AILab-UniversityofTsukuba/Tsukuba-Open-Source-Hand-Prosthesis/Mechanical design/Wrist rotation mechanism/STL/Socket Connector - D_30.STL

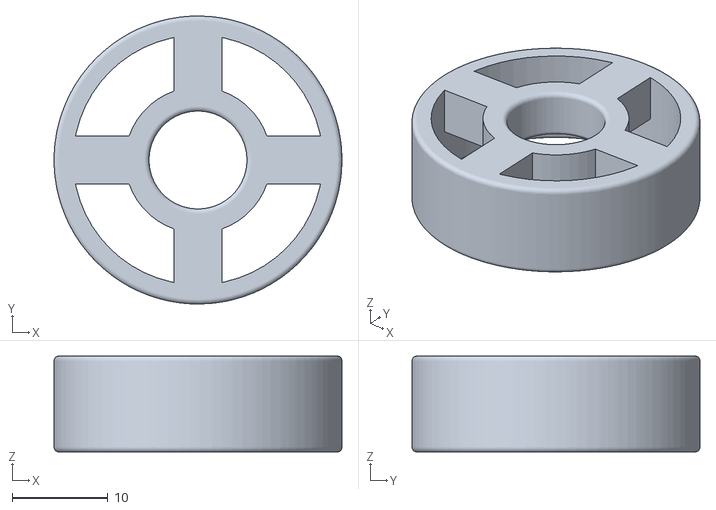
[picture p19: CAD file, 2024-01-24]
Mechanical design/Wrist rotation mechanism/STL/Socket Connector - D_30.STL
30.0 x 30.0 x 10.0
