AILab-UniversityofTsukuba/Tsukuba-Open-Source-Hand-Prosthesis/Mechanical design/Hand /STL/100_R/Thenar eminence - 100_R.STL

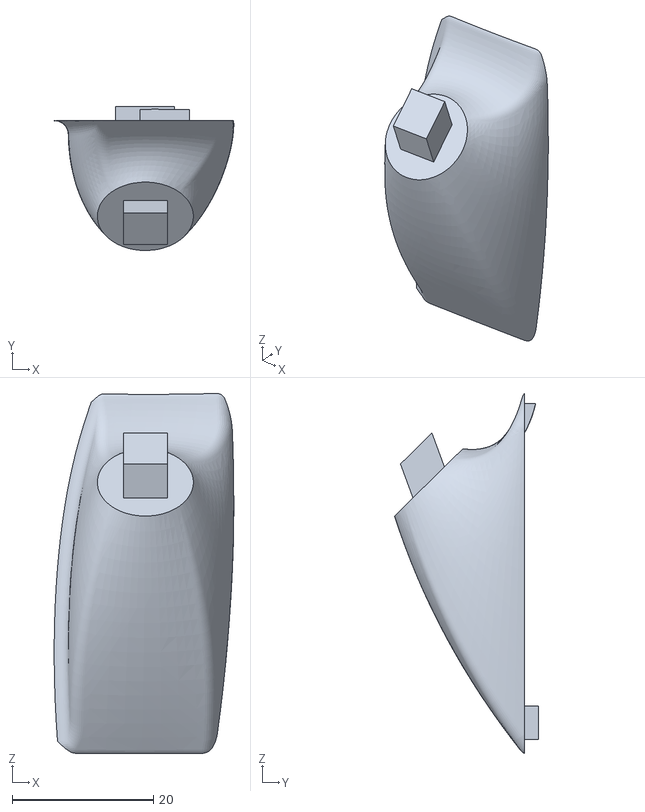
[picture p20: CAD file, 2024-01-24]
Mechanical design/Hand /STL/100_R/Thenar eminence - 100_R.STL
25.4 x 20.4 x 51.0
