AILab-UniversityofTsukuba/Tsukuba-Open-Source-Hand-Prosthesis/Mechanical design/Hand /STL/105_R/Rotation axis - 105_R.STL

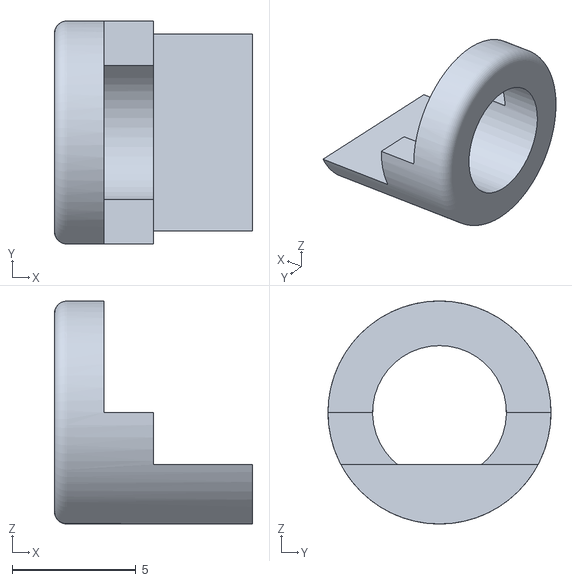
[picture p21: CAD file, 2024-01-24]
Mechanical design/Hand /STL/105_R/Rotation axis - 105_R.STL
8.00 x 9.00 x 9.00
