AILab-UniversityofTsukuba/Tsukuba-Open-Source-Hand-Prosthesis/Mechanical design/Hand /STL/110_R/Ring finger - 110_R.STL

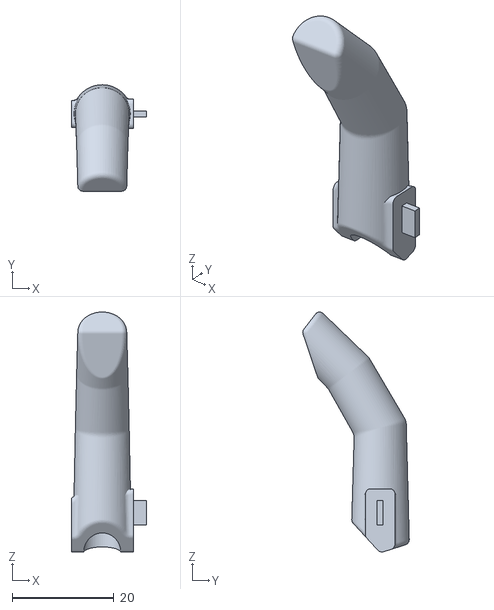
[picture p22: CAD file, 2024-01-24]
Mechanical design/Hand /STL/110_R/Ring finger - 110_R.STL
14.8 x 21.0 x 47.3
