AILab-UniversityofTsukuba/Tsukuba-Open-Source-Hand-Prosthesis/Mechanical design/Hand /STL/115_R/Rotation axis - 115_R.STL

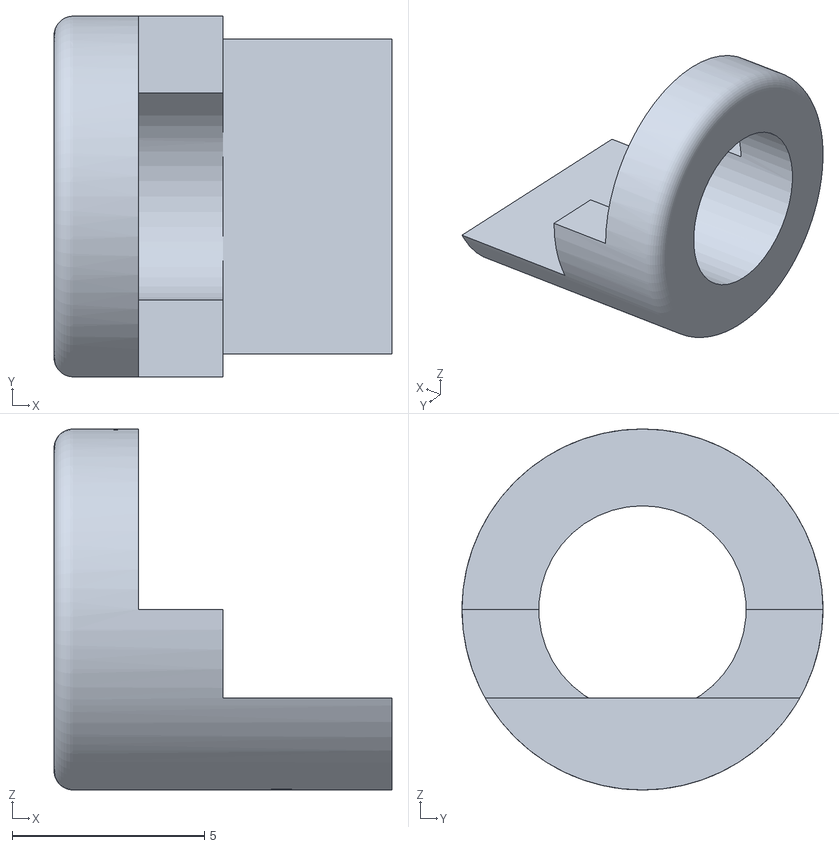
[picture p23: CAD file, 2024-01-24]
Mechanical design/Hand /STL/115_R/Rotation axis - 115_R.STL
8.80 x 9.40 x 9.40
