AILab-UniversityofTsukuba/Tsukuba-Open-Source-Hand-Prosthesis/Mechanical design/Hand /STL/120_R/Index finger - 120_R.STL

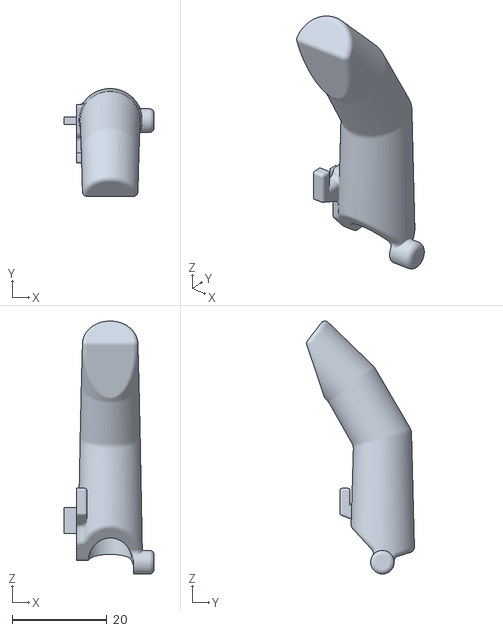
[picture p24: CAD file, 2024-01-24]
Mechanical design/Hand /STL/120_R/Index finger - 120_R.STL
19.1 x 22.8 x 53.4
