AILab-UniversityofTsukuba/Tsukuba-Open-Source-Hand-Prosthesis/Mechanical design/Hand /STL/125_R/Thenar eminence - 125_R.STL

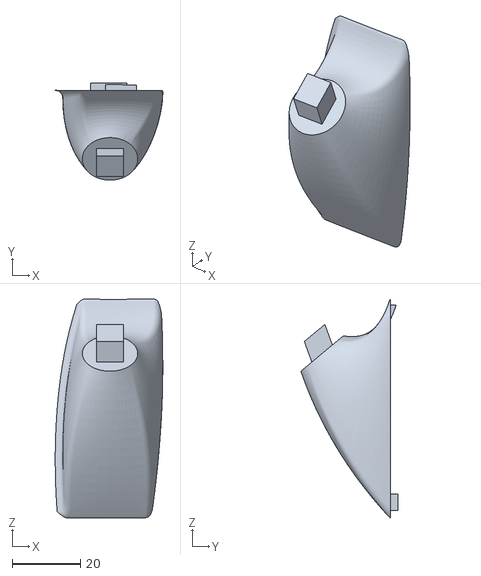
[picture p25: CAD file, 2024-01-24]
Mechanical design/Hand /STL/125_R/Thenar eminence - 125_R.STL
31.5 x 28.5 x 64.1
