AILab-UniversityofTsukuba/Tsukuba-Open-Source-Hand-Prosthesis/Mechanical design/Hand /STL/130_R/Ring finger - 130_R.STL

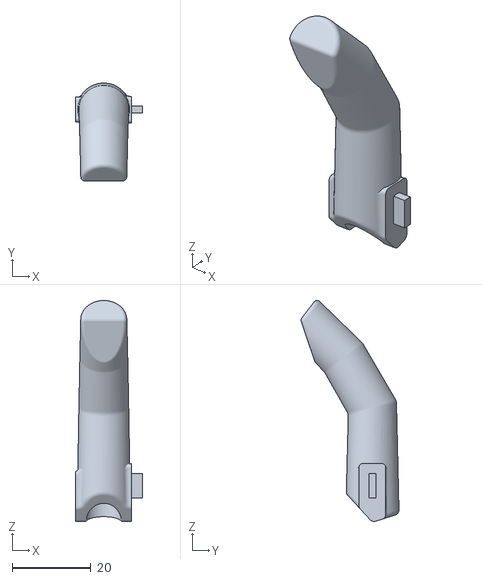
[picture p26: CAD file, 2024-01-24]
Mechanical design/Hand /STL/130_R/Ring finger - 130_R.STL
17.1 x 24.9 x 56.3
