AILab-UniversityofTsukuba/Tsukuba-Open-Source-Hand-Prosthesis/Mechanical design/Hand /STL/135_R/Little finger - 135_R.STL

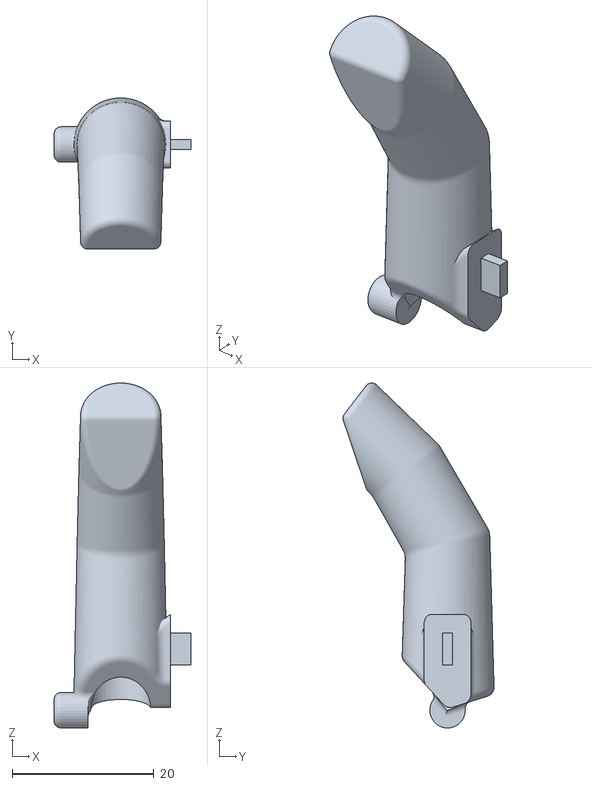
[picture p27: CAD file, 2024-01-24]
Mechanical design/Hand /STL/135_R/Little finger - 135_R.STL
19.3 x 21.3 x 48.6
