AILab-UniversityofTsukuba/Tsukuba-Open-Source-Hand-Prosthesis/Mechanical design/Hand /STL/140_R/Thenar eminence - 140_R.STL

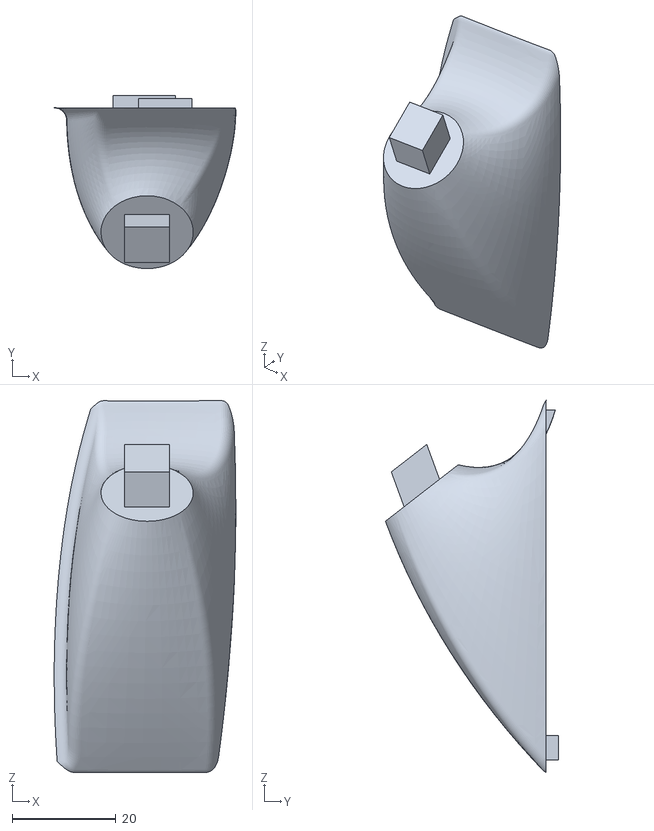
[picture p28: CAD file, 2024-01-24]
Mechanical design/Hand /STL/140_R/Thenar eminence - 140_R.STL
35.1 x 33.4 x 71.8
