AILab-UniversityofTsukuba/Tsukuba-Open-Source-Hand-Prosthesis/Mechanical design/Hand /STL/145_R/Ring finger - 145_R.STL

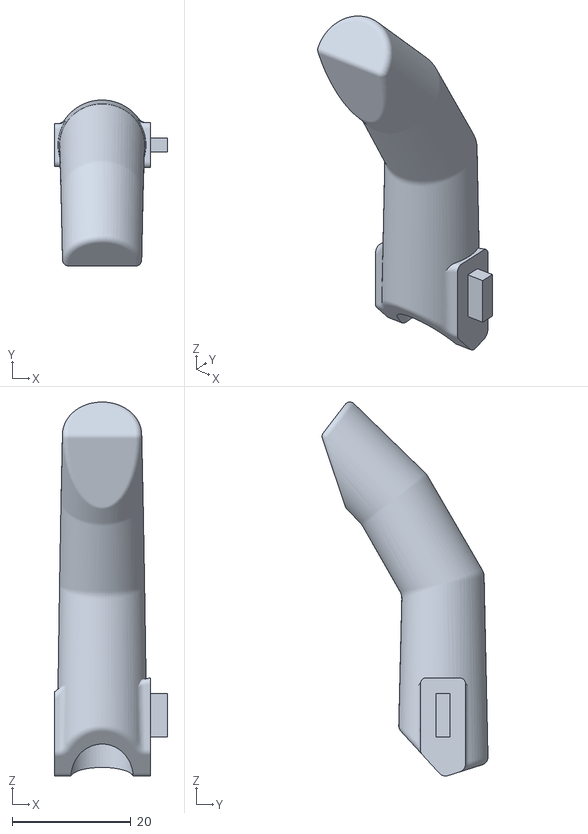
[picture p29: CAD file, 2024-01-24]
Mechanical design/Hand /STL/145_R/Ring finger - 145_R.STL
19.0 x 27.9 x 62.9
