AILab-UniversityofTsukuba/Tsukuba-Open-Source-Hand-Prosthesis/Mechanical design/Hand /STL/150_R/Lid - 150_R.STL

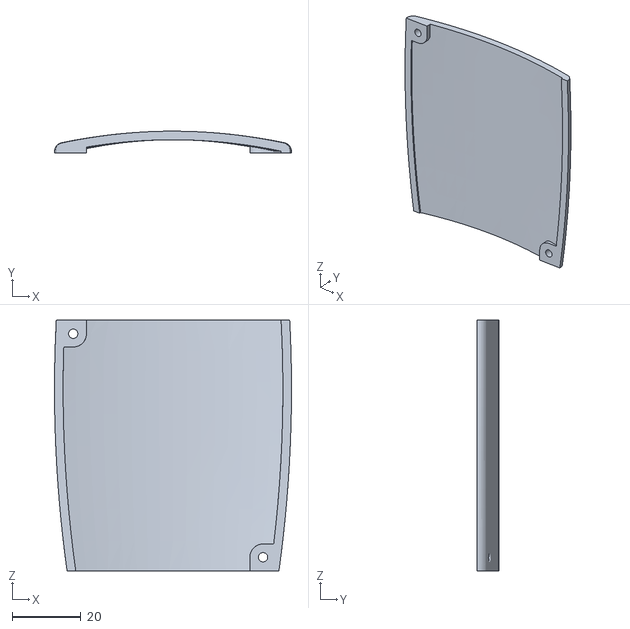
[picture p30: CAD file, 2024-01-24]
Mechanical design/Hand /STL/150_R/Lid - 150_R.STL
68.8 x 6.30 x 72.8
