AILab-UniversityofTsukuba/Tsukuba-Open-Source-Hand-Prosthesis/Mechanical design/Wrist rotation mechanism/STL/Socket Connector - D_35.STL

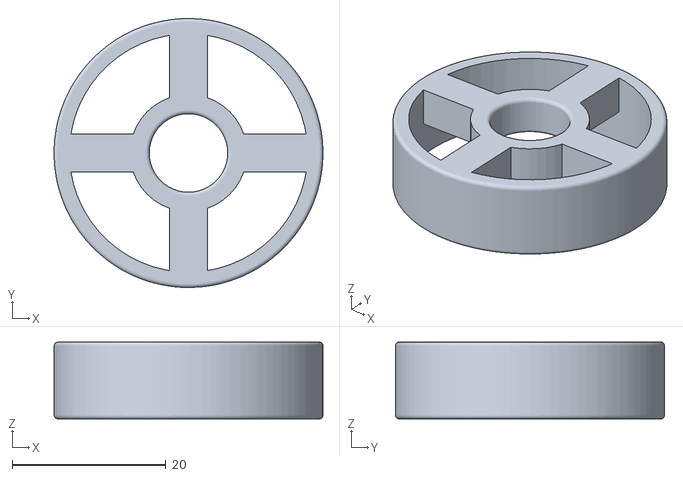
[picture p31: CAD file, 2024-01-24]
Mechanical design/Wrist rotation mechanism/STL/Socket Connector - D_35.STL
35.0 x 35.0 x 10.0
