AILab-UniversityofTsukuba/Tsukuba-Open-Source-Hand-Prosthesis/Mechanical design/Hand /CAD/Palm_structure_5.SLDPRT

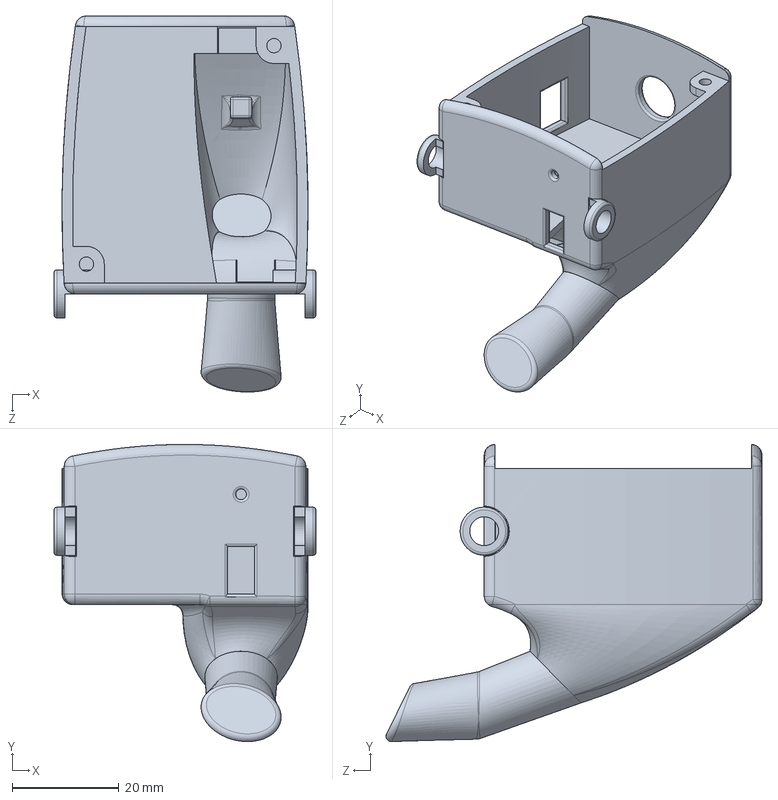
[picture p32: CAD file, 2024-01-24]
Mechanical design/Hand /CAD/Palm_structure_5.SLDPRT
49.0 x 55.6 x 70.4 mm
