AILab-UniversityofTsukuba/Tsukuba-Open-Source-Hand-Prosthesis/Mechanical design/Hand /STL/100_R/Middle finger - 100_R.STL

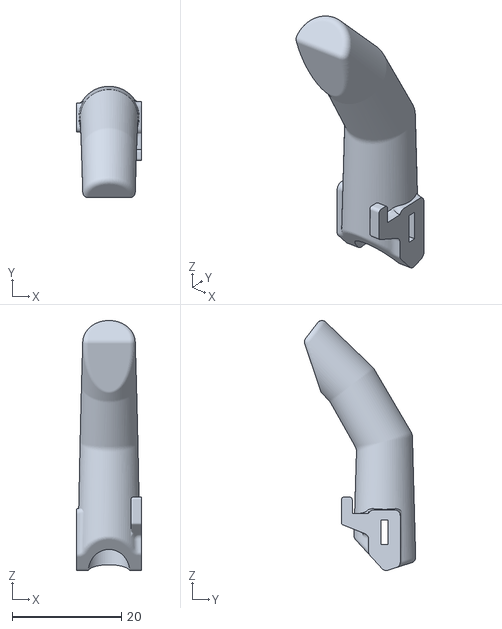
[picture p33: CAD file, 2024-01-24]
Mechanical design/Hand /STL/100_R/Middle finger - 100_R.STL
12.0 x 20.4 x 45.8
