AILab-UniversityofTsukuba/Tsukuba-Open-Source-Hand-Prosthesis/Mechanical design/Hand /STL/105_R/Middle finger - 105_R.STL

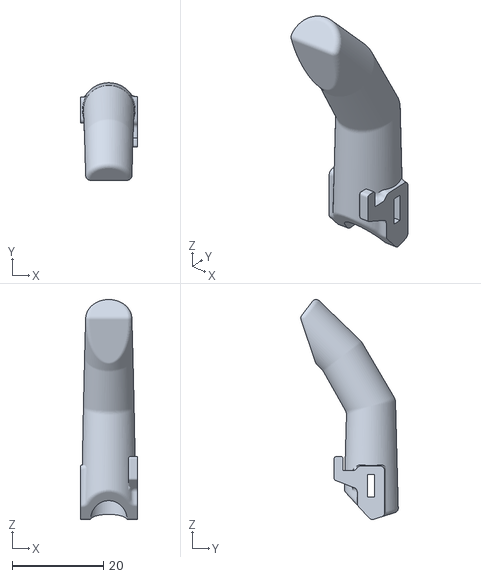
[picture p34: CAD file, 2024-01-24]
Mechanical design/Hand /STL/105_R/Middle finger - 105_R.STL
12.5 x 21.4 x 48.2
