AILab-UniversityofTsukuba/Tsukuba-Open-Source-Hand-Prosthesis/Mechanical design/Hand /STL/110_R/Palm - 110_R.STL

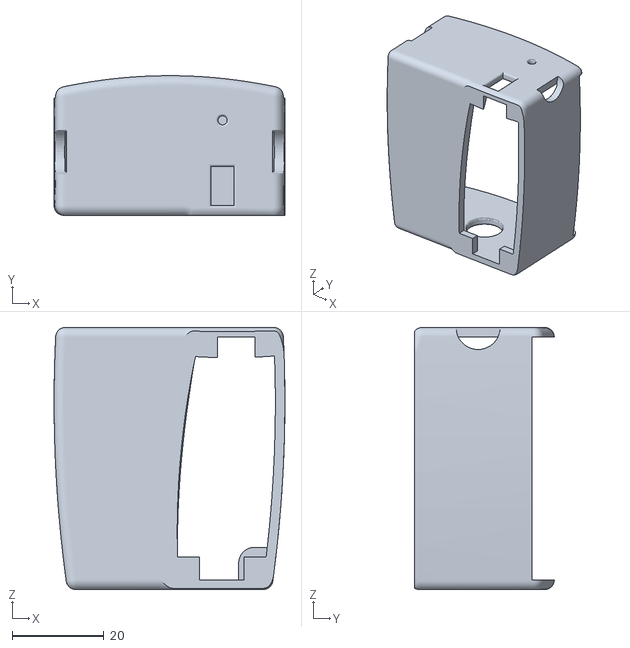
[picture p35: CAD file, 2024-01-24]
Mechanical design/Hand /STL/110_R/Palm - 110_R.STL
50.4 x 30.5 x 57.2
