AILab-UniversityofTsukuba/Tsukuba-Open-Source-Hand-Prosthesis/Mechanical design/Hand /STL/115_R/Little finger - 115_R.STL

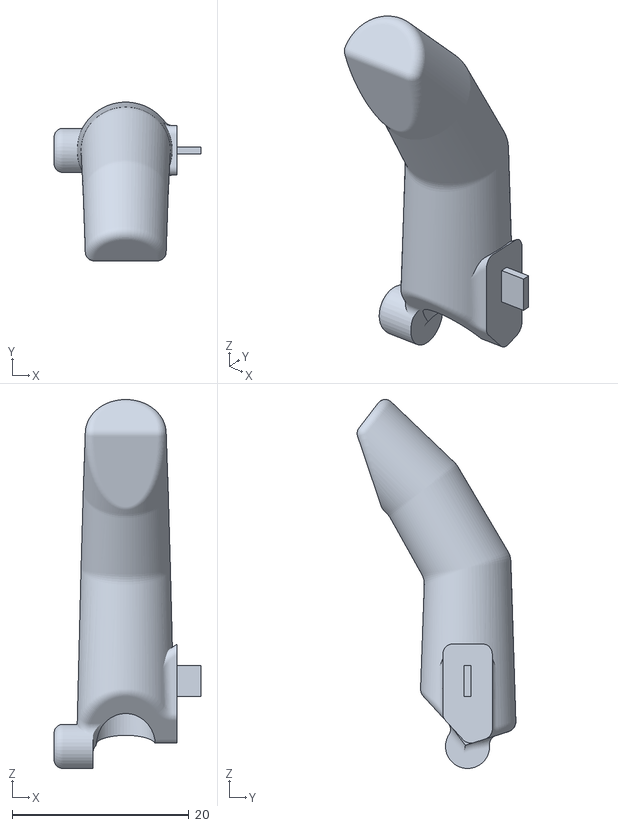
[picture p36: CAD file, 2024-01-24]
Mechanical design/Hand /STL/115_R/Little finger - 115_R.STL
16.6 x 17.9 x 41.7
