AILab-UniversityofTsukuba/Tsukuba-Open-Source-Hand-Prosthesis/Mechanical design/Hand /STL/120_R/Thumb - 120_R.STL

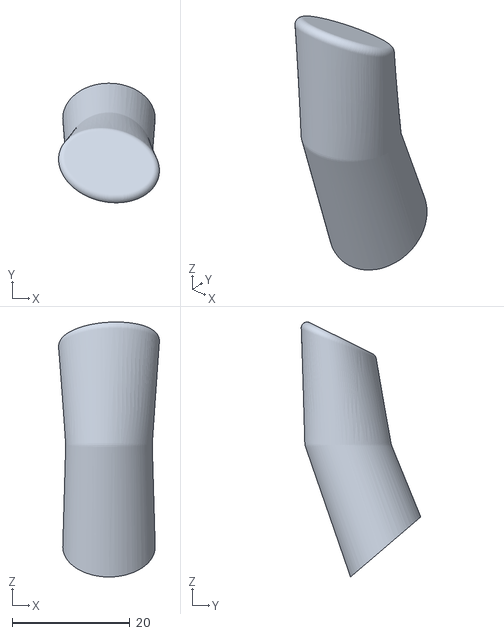
[picture p37: CAD file, 2024-01-24]
Mechanical design/Hand /STL/120_R/Thumb - 120_R.STL
17.1 x 20.3 x 43.3
