AILab-UniversityofTsukuba/Tsukuba-Open-Source-Hand-Prosthesis/Mechanical design/Hand /STL/125_R/Thumb - 125_R.STL

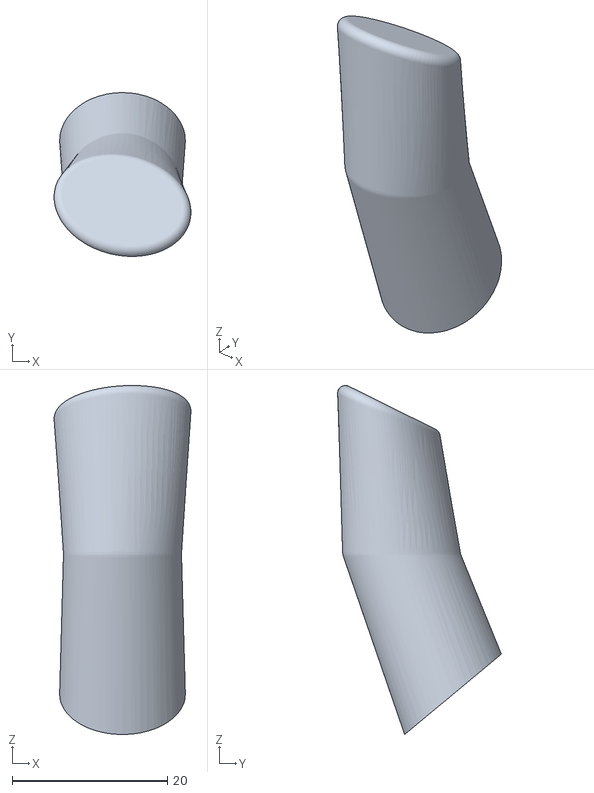
[picture p38: CAD file, 2024-01-24]
Mechanical design/Hand /STL/125_R/Thumb - 125_R.STL
17.6 x 21.1 x 44.9
