AILab-UniversityofTsukuba/Tsukuba-Open-Source-Hand-Prosthesis/Mechanical design/Hand /STL/130_R/Lid - 130_R.STL

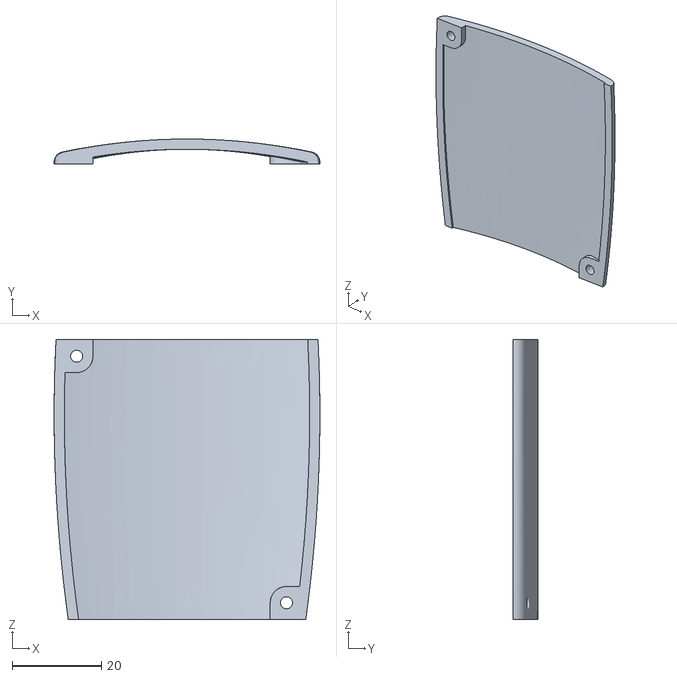
[picture p39: CAD file, 2024-01-24]
Mechanical design/Hand /STL/130_R/Lid - 130_R.STL
59.6 x 5.60 x 62.8
