AILab-UniversityofTsukuba/Tsukuba-Open-Source-Hand-Prosthesis/Mechanical design/Hand /STL/135_R/Thumb - 135_R.STL

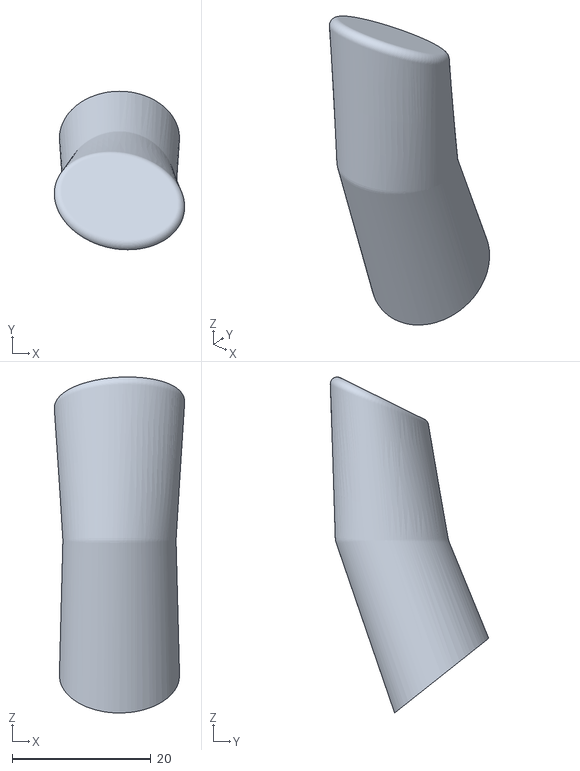
[picture p40: CAD file, 2024-01-24]
Mechanical design/Hand /STL/135_R/Thumb - 135_R.STL
18.8 x 22.8 x 48.4
