AILab-UniversityofTsukuba/Tsukuba-Open-Source-Hand-Prosthesis/Mechanical design/Hand /STL/140_R/Palm - 140_R.STL

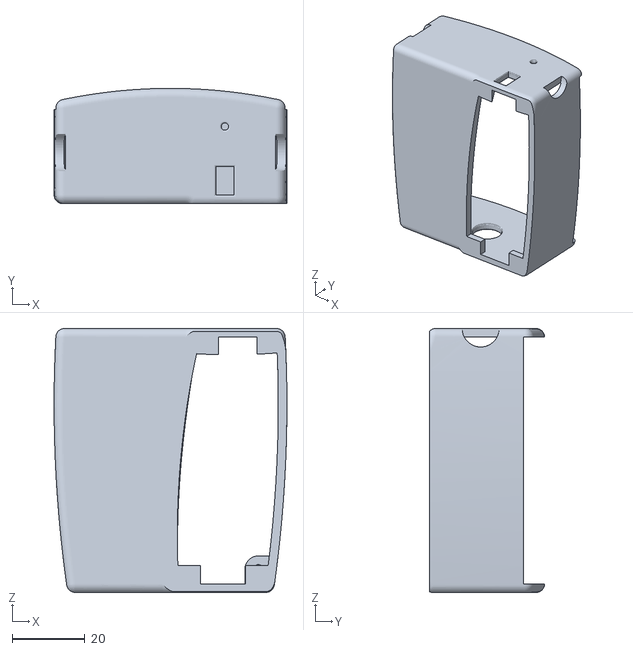
[picture p41: CAD file, 2024-01-24]
Mechanical design/Hand /STL/140_R/Palm - 140_R.STL
64.2 x 31.8 x 72.8
