AILab-UniversityofTsukuba/Tsukuba-Open-Source-Hand-Prosthesis/Mechanical design/Hand /STL/145_R/Rotation axis - 145_R.STL

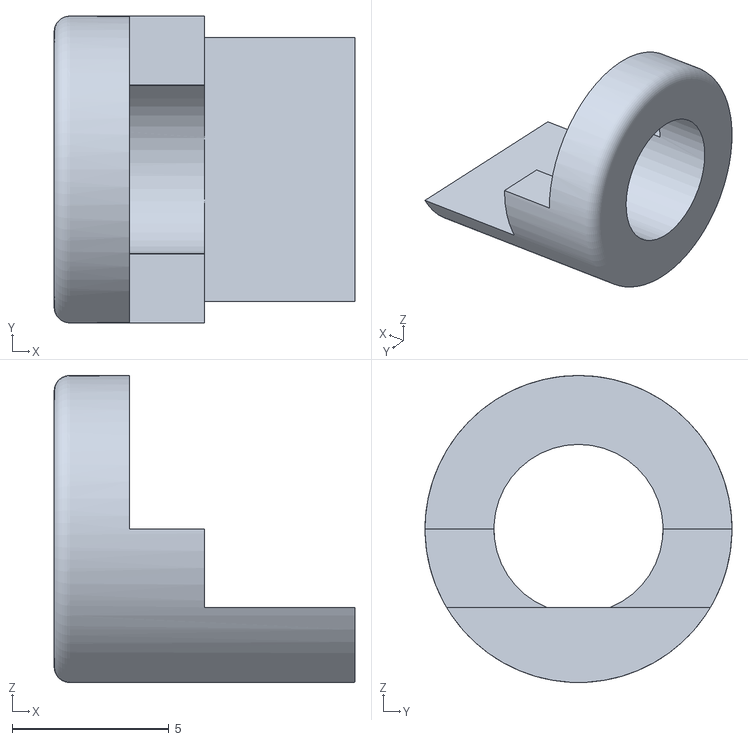
[picture p42: CAD file, 2024-01-24]
Mechanical design/Hand /STL/145_R/Rotation axis - 145_R.STL
9.60 x 9.80 x 9.80
