AILab-UniversityofTsukuba/Tsukuba-Open-Source-Hand-Prosthesis/Mechanical design/Hand /STL/150_R/Index finger - 150_R.STL

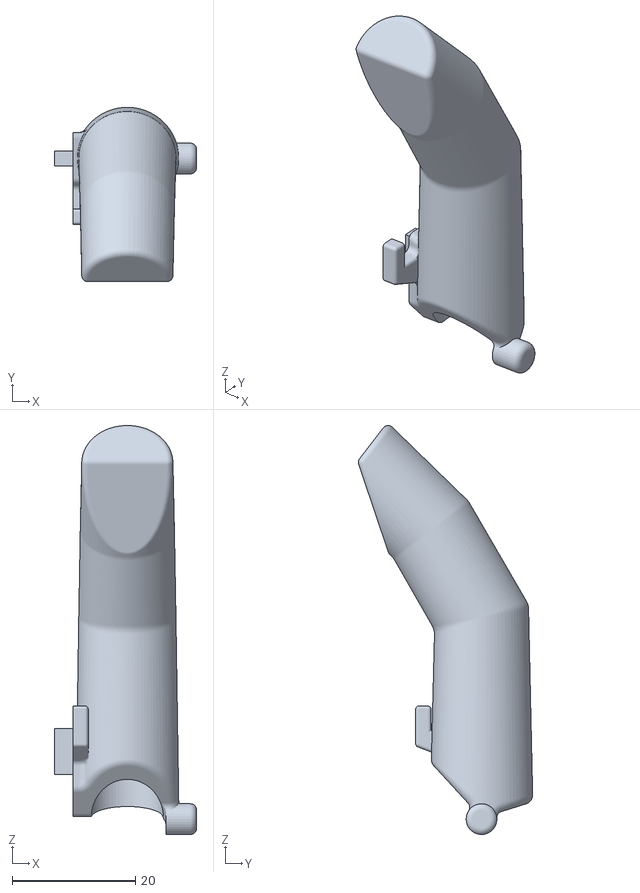
[picture p43: CAD file, 2024-01-24]
Mechanical design/Hand /STL/150_R/Index finger - 150_R.STL
23.1 x 28.3 x 66.5
