AILab-UniversityofTsukuba/Tsukuba-Open-Source-Hand-Prosthesis/Mechanical design/Hand /STL/105_R/Thenar eminence - 105_R.STL

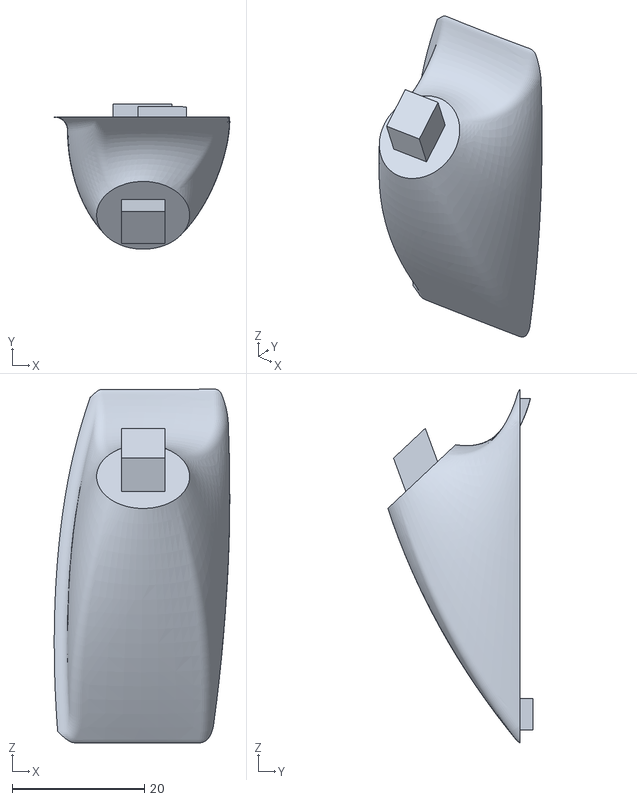
[picture p44: CAD file, 2024-01-24]
Mechanical design/Hand /STL/105_R/Thenar eminence - 105_R.STL
26.6 x 22.0 x 53.6
