AILab-UniversityofTsukuba/Tsukuba-Open-Source-Hand-Prosthesis/Mechanical design/Hand /STL/110_R/Lid - 110_R.STL

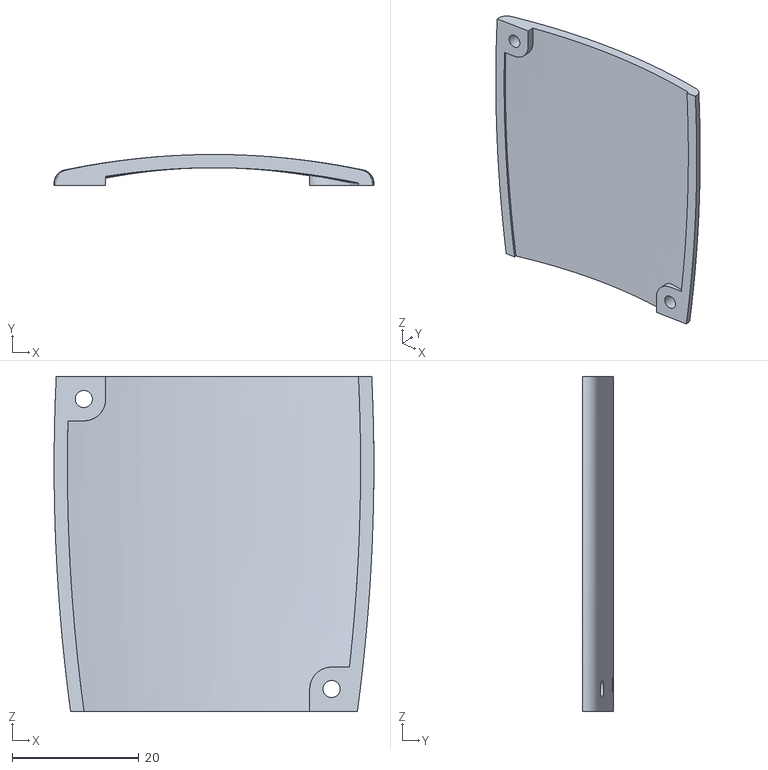
[picture p45: CAD file, 2024-01-24]
Mechanical design/Hand /STL/110_R/Lid - 110_R.STL
50.4 x 4.90 x 52.8
