AILab-UniversityofTsukuba/Tsukuba-Open-Source-Hand-Prosthesis/Mechanical design/Hand /STL/115_R/Thenar eminence - 115_R.STL

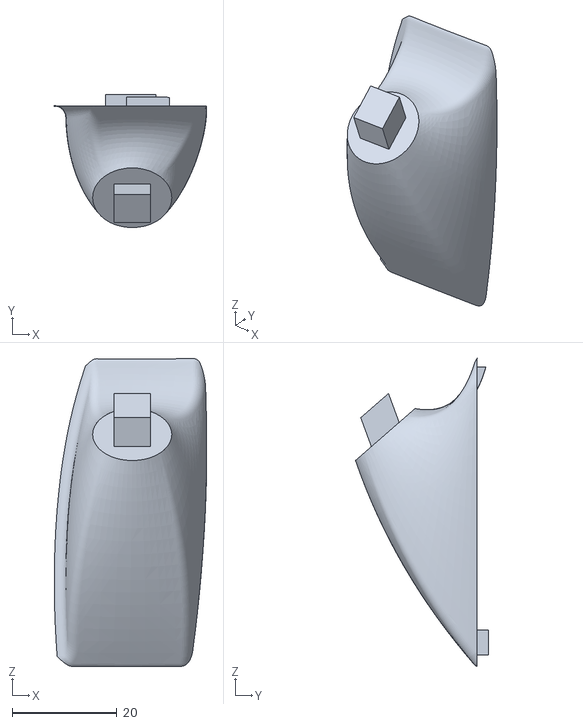
[picture p46: CAD file, 2024-01-24]
Mechanical design/Hand /STL/115_R/Thenar eminence - 115_R.STL
29.1 x 25.4 x 58.8
