AILab-UniversityofTsukuba/Tsukuba-Open-Source-Hand-Prosthesis/Mechanical design/Hand /STL/120_R/Lid - 120_R.STL

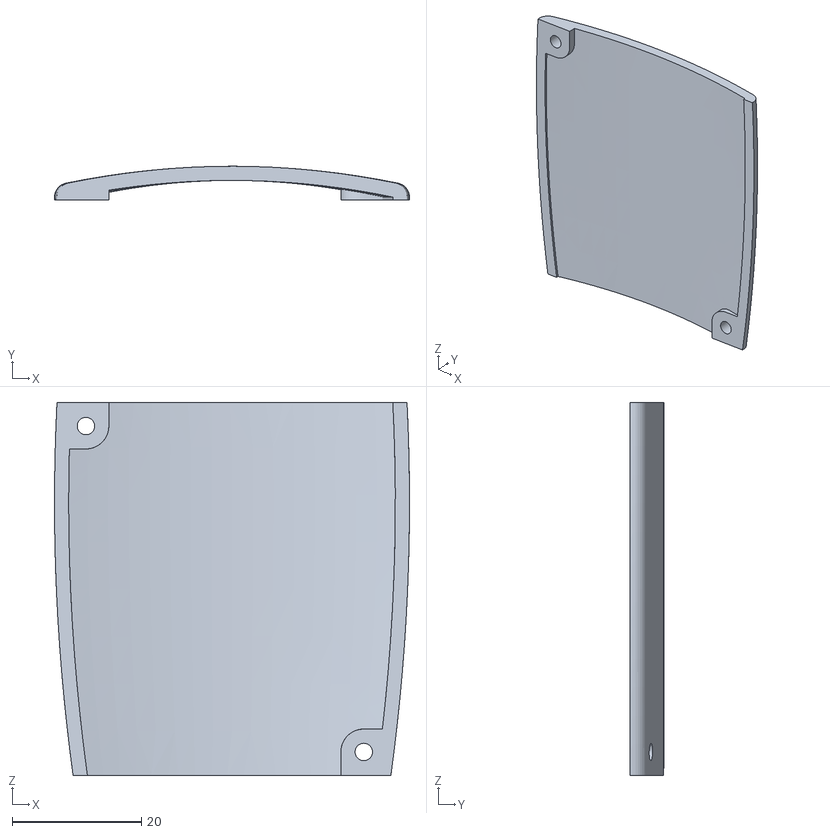
[picture p47: CAD file, 2024-01-24]
Mechanical design/Hand /STL/120_R/Lid - 120_R.STL
55.0 x 5.20 x 57.8
