AILab-UniversityofTsukuba/Tsukuba-Open-Source-Hand-Prosthesis/Mechanical design/Hand /STL/125_R/Middle finger - 125_R.STL

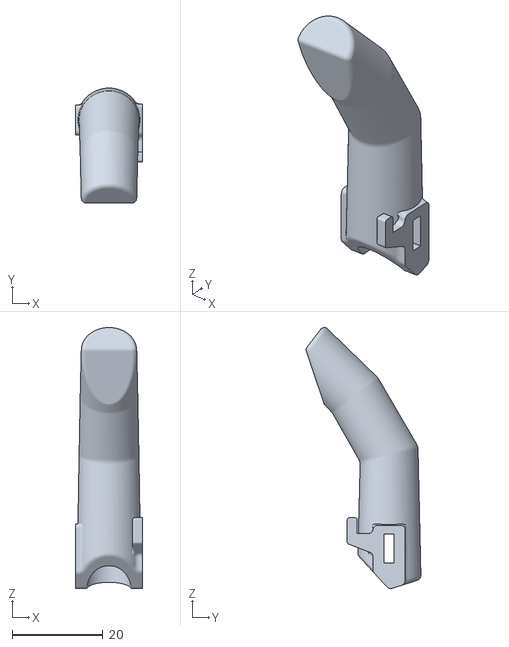
[picture p48: CAD file, 2024-01-24]
Mechanical design/Hand /STL/125_R/Middle finger - 125_R.STL
14.8 x 25.3 x 57.6
