AILab-UniversityofTsukuba/Tsukuba-Open-Source-Hand-Prosthesis/Mechanical design/Hand /STL/130_R/Index finger - 130_R.STL

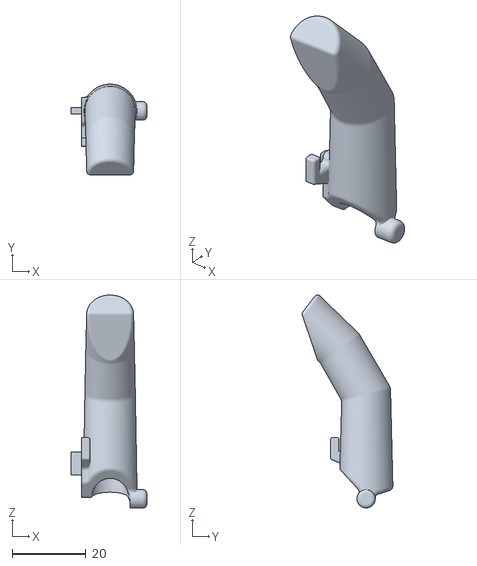
[picture p49: CAD file, 2024-01-24]
Mechanical design/Hand /STL/130_R/Index finger - 130_R.STL
20.5 x 24.6 x 57.8
