AILab-UniversityofTsukuba/Tsukuba-Open-Source-Hand-Prosthesis/Mechanical design/Hand /STL/135_R/Lid - 135_R.STL

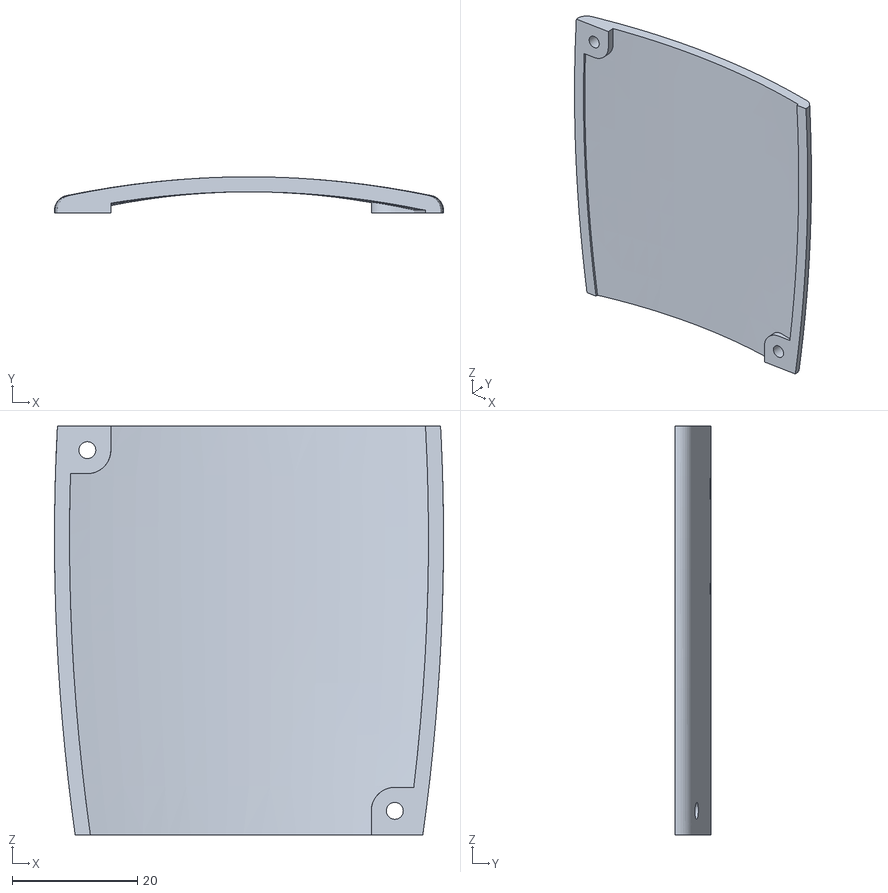
[picture p50: CAD file, 2024-01-24]
Mechanical design/Hand /STL/135_R/Lid - 135_R.STL
62.0 x 5.80 x 65.2
