AILab-UniversityofTsukuba/Tsukuba-Open-Source-Hand-Prosthesis/Mechanical design/Hand /STL/140_R/Ring finger - 140_R.STL

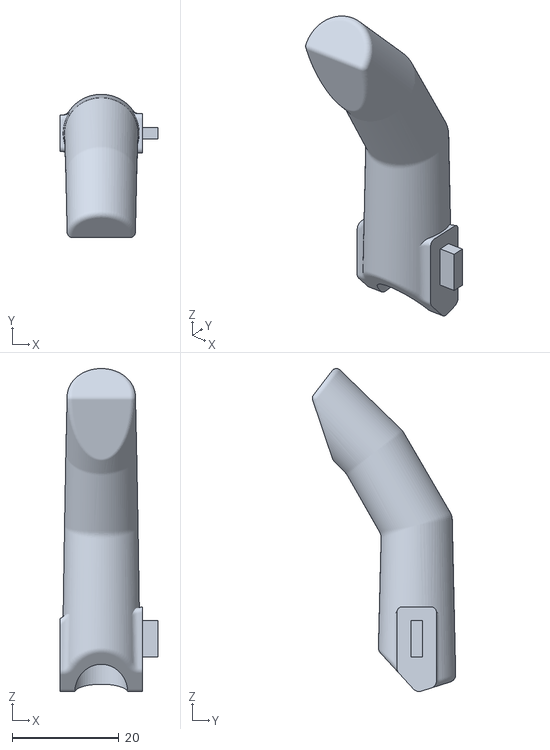
[picture p51: CAD file, 2024-01-24]
Mechanical design/Hand /STL/140_R/Ring finger - 140_R.STL
18.4 x 26.9 x 60.6
