AILab-UniversityofTsukuba/Tsukuba-Open-Source-Hand-Prosthesis/Mechanical design/Hand /STL/145_R/Lid - 145_R.STL

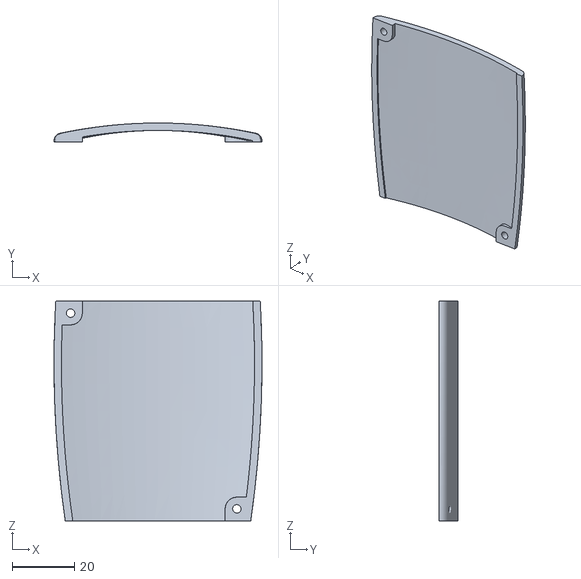
[picture p52: CAD file, 2024-01-24]
Mechanical design/Hand /STL/145_R/Lid - 145_R.STL
66.6 x 6.10 x 70.4
