AILab-UniversityofTsukuba/Tsukuba-Open-Source-Hand-Prosthesis/Mechanical design/Hand /STL/150_R/Little finger - 150_R.STL

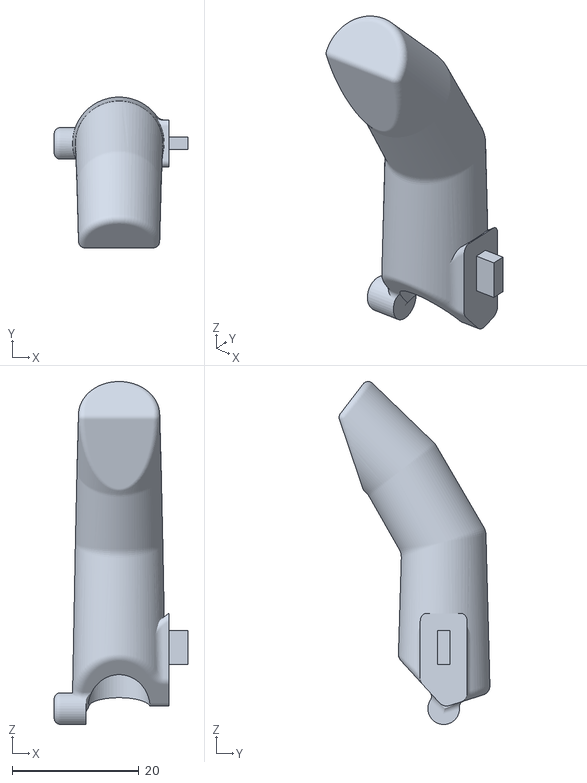
[picture p53: CAD file, 2024-01-24]
Mechanical design/Hand /STL/150_R/Little finger - 150_R.STL
21.1 x 23.8 x 54.1
