AILab-UniversityofTsukuba/Tsukuba-Open-Source-Hand-Prosthesis/Mechanical design/Wrist rotation mechanism/STL/Socket Connector - D_20.STL

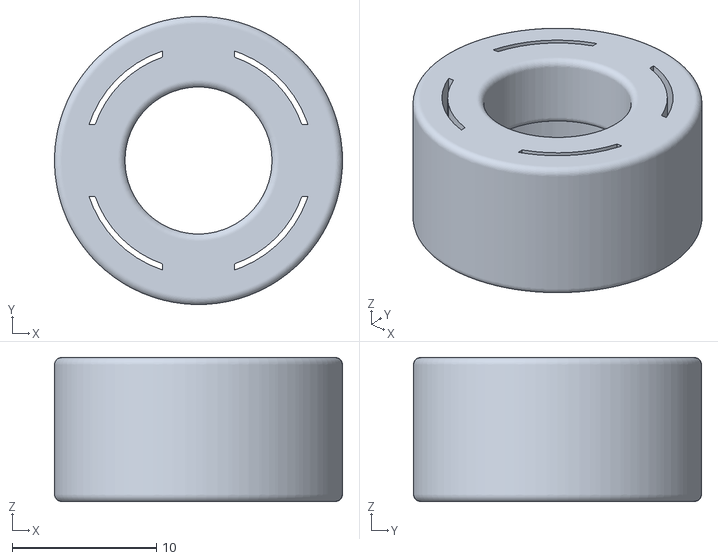
[picture p54: CAD file, 2024-01-24]
Mechanical design/Wrist rotation mechanism/STL/Socket Connector - D_20.STL
20.0 x 20.0 x 10.0
