AILab-UniversityofTsukuba/Tsukuba-Open-Source-Hand-Prosthesis/Mechanical design/Hand /STL/100_R/Lid - 100_R.STL

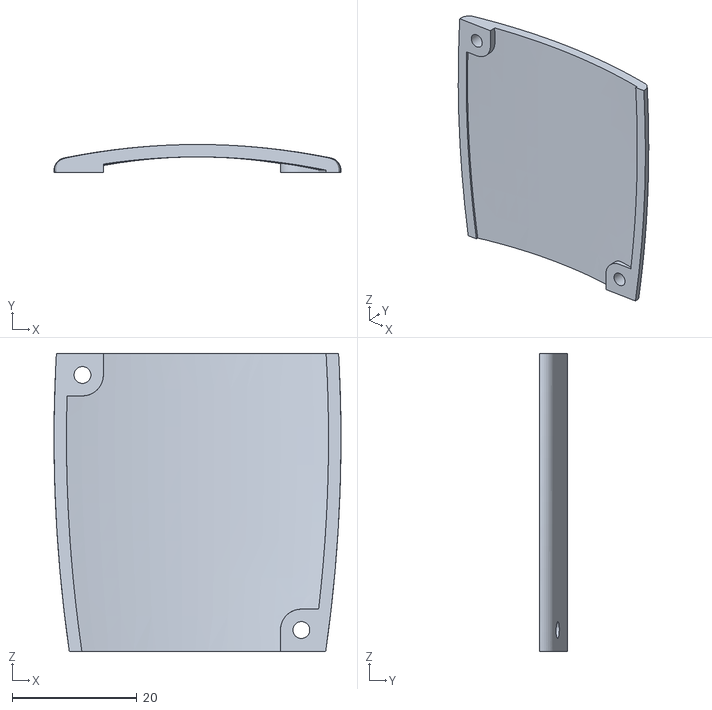
[picture p55: CAD file, 2024-01-24]
Mechanical design/Hand /STL/100_R/Lid - 100_R.STL
46.0 x 4.50 x 47.8
