AILab-UniversityofTsukuba/Tsukuba-Open-Source-Hand-Prosthesis/Mechanical design/Hand /STL/105_R/Ring finger - 105_R.STL

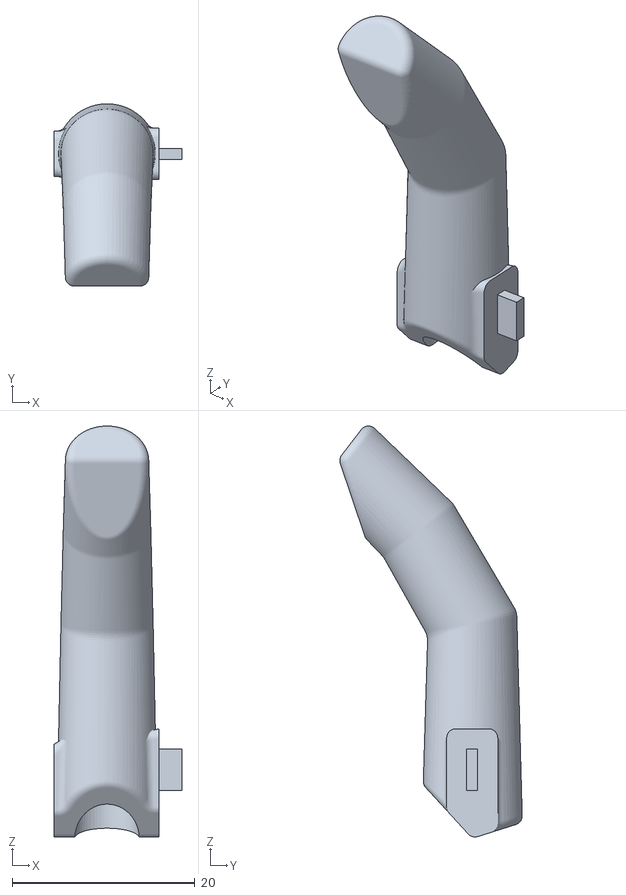
[picture p56: CAD file, 2024-01-24]
Mechanical design/Hand /STL/105_R/Ring finger - 105_R.STL
14.0 x 20.0 x 45.0
