AILab-UniversityofTsukuba/Tsukuba-Open-Source-Hand-Prosthesis/Mechanical design/Hand /STL/110_R/Thenar eminence - 110_R.STL

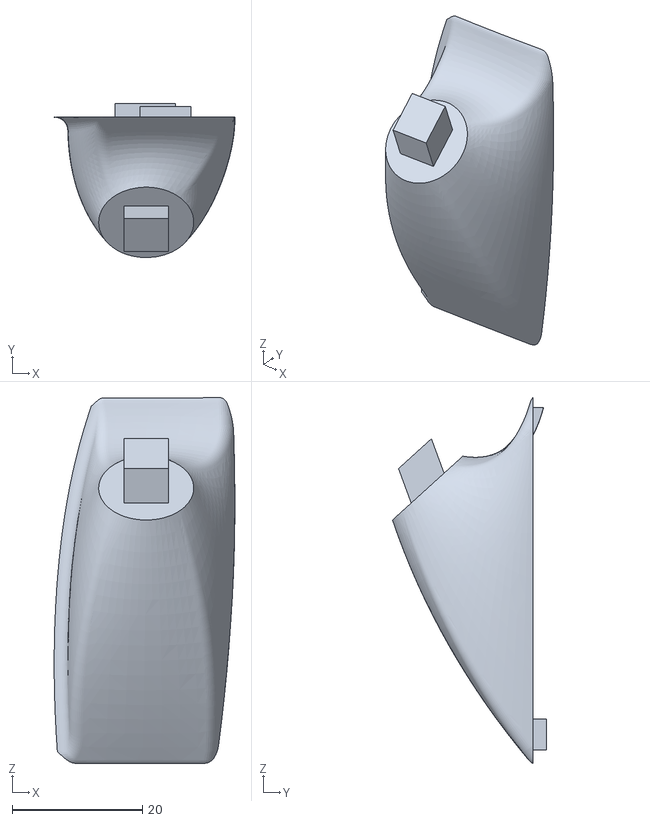
[picture p57: CAD file, 2024-01-24]
Mechanical design/Hand /STL/110_R/Thenar eminence - 110_R.STL
27.8 x 23.7 x 56.2
