AILab-UniversityofTsukuba/Tsukuba-Open-Source-Hand-Prosthesis/Mechanical design/Hand /STL/115_R/Middle finger - 115_R.STL

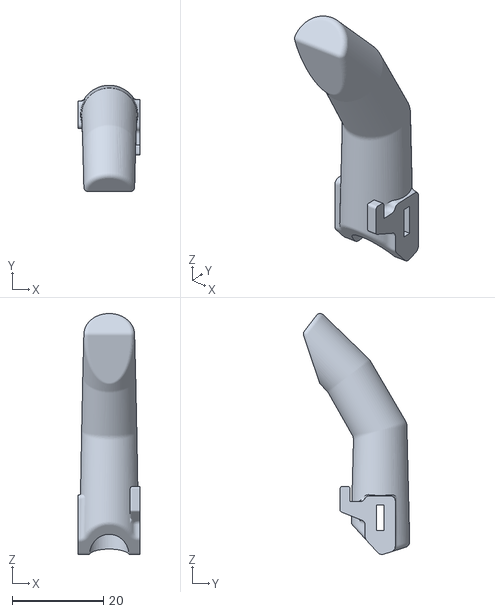
[picture p58: CAD file, 2024-01-24]
Mechanical design/Hand /STL/115_R/Middle finger - 115_R.STL
13.7 x 23.3 x 52.8
