AILab-UniversityofTsukuba/Tsukuba-Open-Source-Hand-Prosthesis/Mechanical design/Hand /STL/125_R/Index finger - 125_R.STL

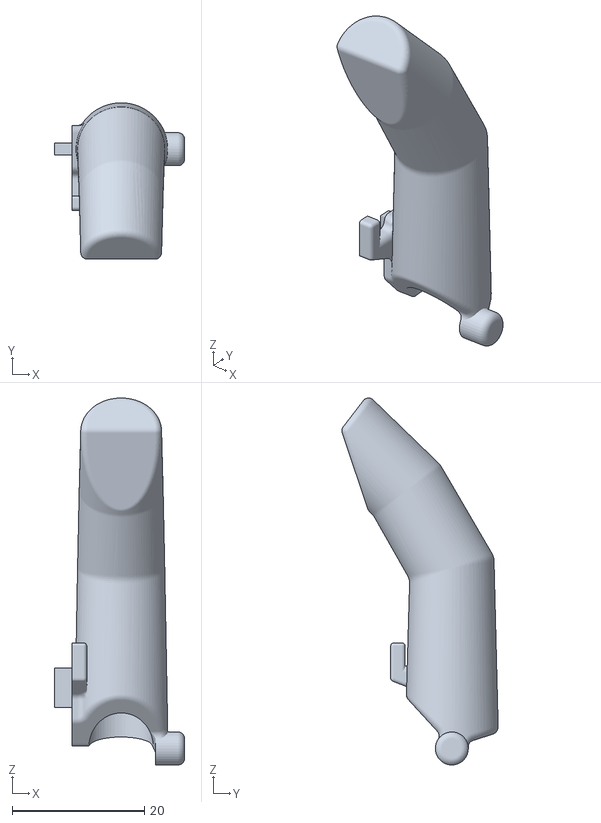
[picture p59: CAD file, 2024-01-24]
Mechanical design/Hand /STL/125_R/Index finger - 125_R.STL
19.7 x 23.7 x 55.5
