AILab-UniversityofTsukuba/Tsukuba-Open-Source-Hand-Prosthesis/Mechanical design/Hand /STL/130_R/Little finger - 130_R.STL

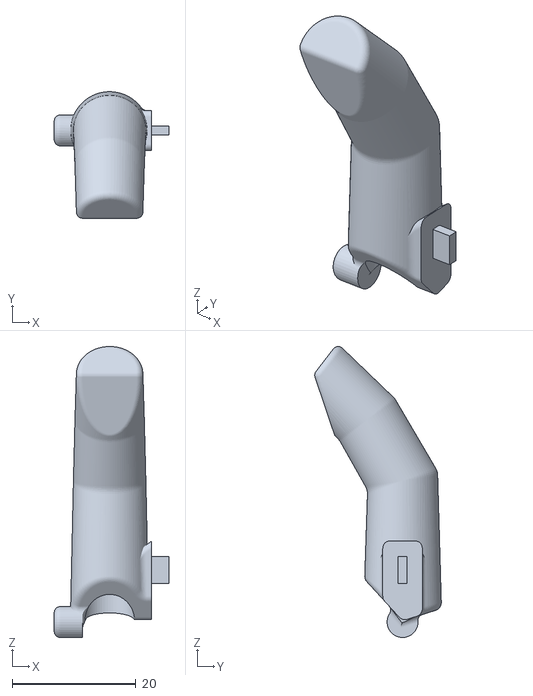
[picture p60: CAD file, 2024-01-24]
Mechanical design/Hand /STL/130_R/Little finger - 130_R.STL
18.5 x 20.4 x 47.0
