AILab-UniversityofTsukuba/Tsukuba-Open-Source-Hand-Prosthesis/Mechanical design/Hand /STL/135_R/Ring finger - 135_R.STL

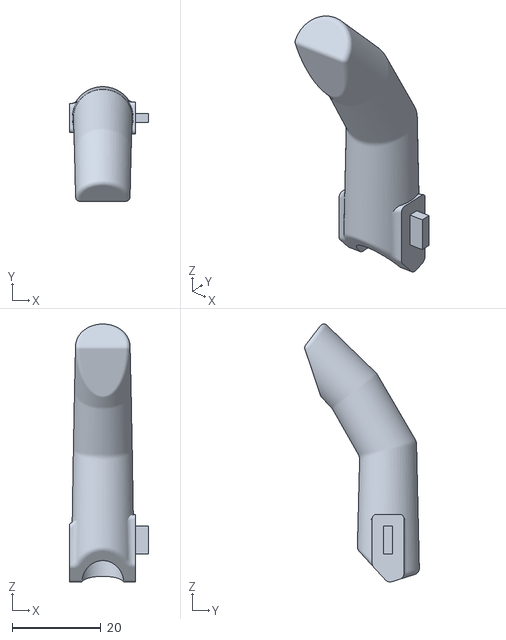
[picture p61: CAD file, 2024-01-24]
Mechanical design/Hand /STL/135_R/Ring finger - 135_R.STL
17.8 x 25.9 x 58.3
