AILab-UniversityofTsukuba/Tsukuba-Open-Source-Hand-Prosthesis/Mechanical design/Hand /STL/140_R/Middle finger - 140_R.STL

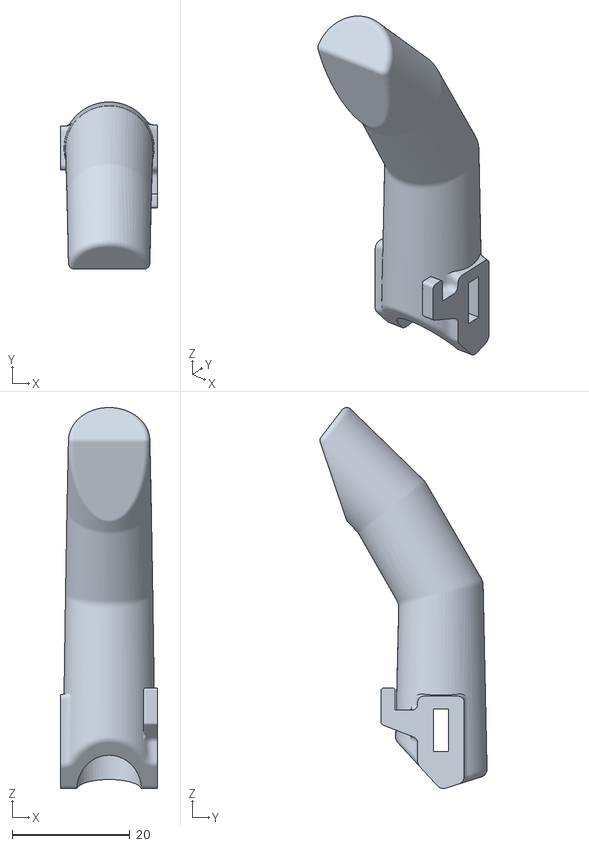
[picture p62: CAD file, 2024-01-24]
Mechanical design/Hand /STL/140_R/Middle finger - 140_R.STL
16.4 x 28.3 x 64.6
