AILab-UniversityofTsukuba/Tsukuba-Open-Source-Hand-Prosthesis/Mechanical design/Hand /STL/145_R/Middle finger - 145_R.STL

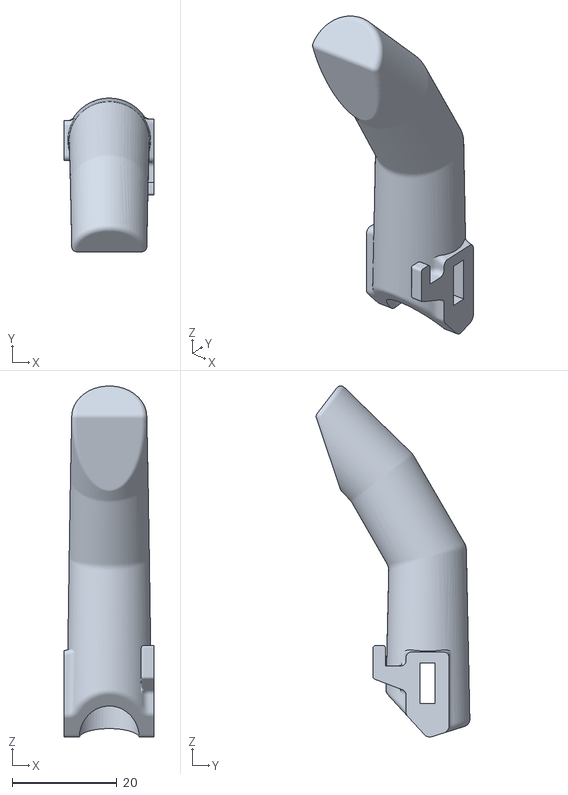
[picture p63: CAD file, 2024-01-24]
Mechanical design/Hand /STL/145_R/Middle finger - 145_R.STL
17.1 x 29.3 x 66.9
