AILab-UniversityofTsukuba/Tsukuba-Open-Source-Hand-Prosthesis/Mechanical design/Hand /STL/150_R/Ring finger - 150_R.STL

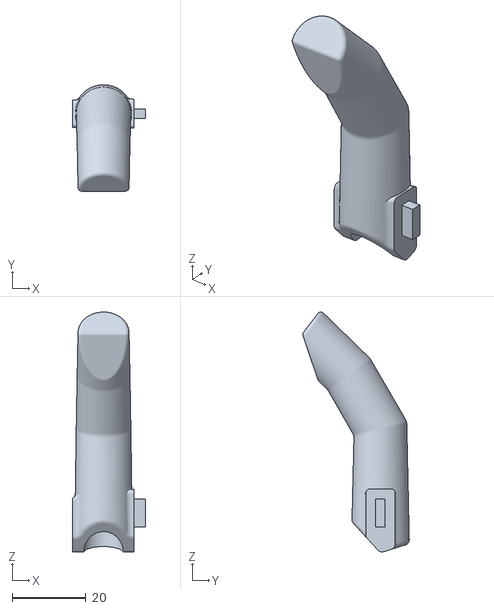
[picture p64: CAD file, 2024-01-24]
Mechanical design/Hand /STL/150_R/Ring finger - 150_R.STL
19.6 x 28.8 x 64.9
