AILab-UniversityofTsukuba/Tsukuba-Open-Source-Hand-Prosthesis/Mechanical design/Wrist rotation mechanism/STL/Socket Connector - D_25.STL

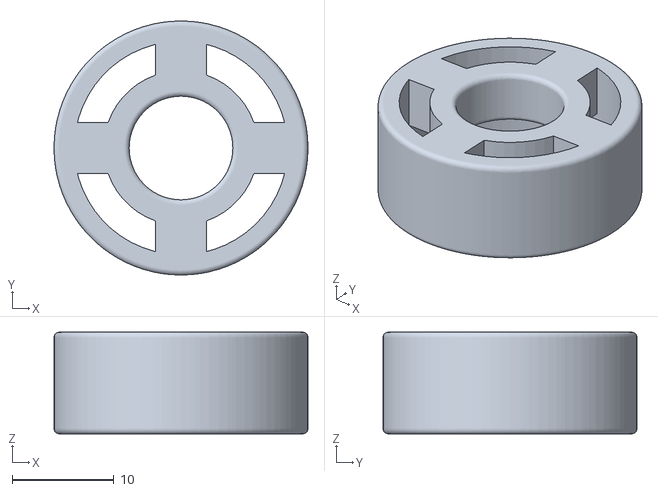
[picture p65: CAD file, 2024-01-24]
Mechanical design/Wrist rotation mechanism/STL/Socket Connector - D_25.STL
25.0 x 25.0 x 10.0
