AILab-UniversityofTsukuba/Tsukuba-Open-Source-Hand-Prosthesis/Mechanical design/Hand /STL/100_R/Index finger - 100_R.STL

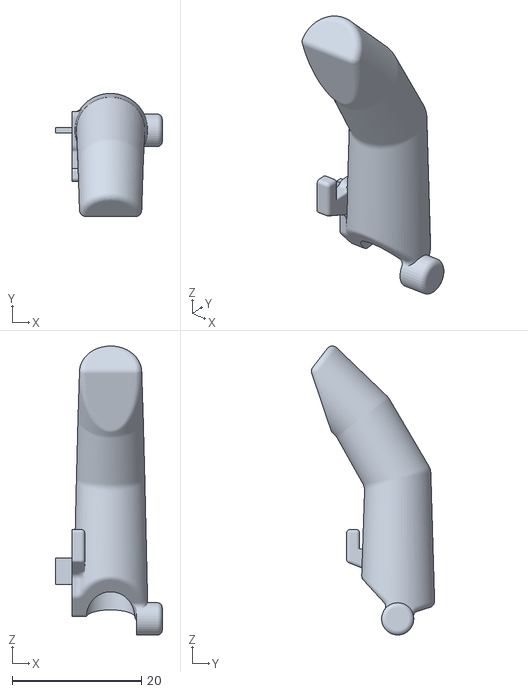
[picture p66: CAD file, 2024-01-24]
Mechanical design/Hand /STL/100_R/Index finger - 100_R.STL
16.5 x 19.1 x 44.8
