AILab-UniversityofTsukuba/Tsukuba-Open-Source-Hand-Prosthesis/Mechanical design/Hand /STL/105_R/Palm - 105_R.STL

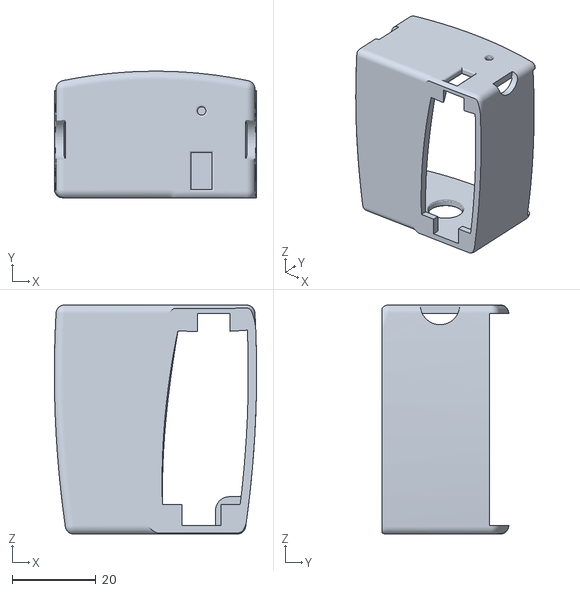
[picture p67: CAD file, 2024-01-24]
Mechanical design/Hand /STL/105_R/Palm - 105_R.STL
48.2 x 30.2 x 54.6
