AILab-UniversityofTsukuba/Tsukuba-Open-Source-Hand-Prosthesis/Mechanical design/Hand /STL/110_R/Thumb - 110_R.STL

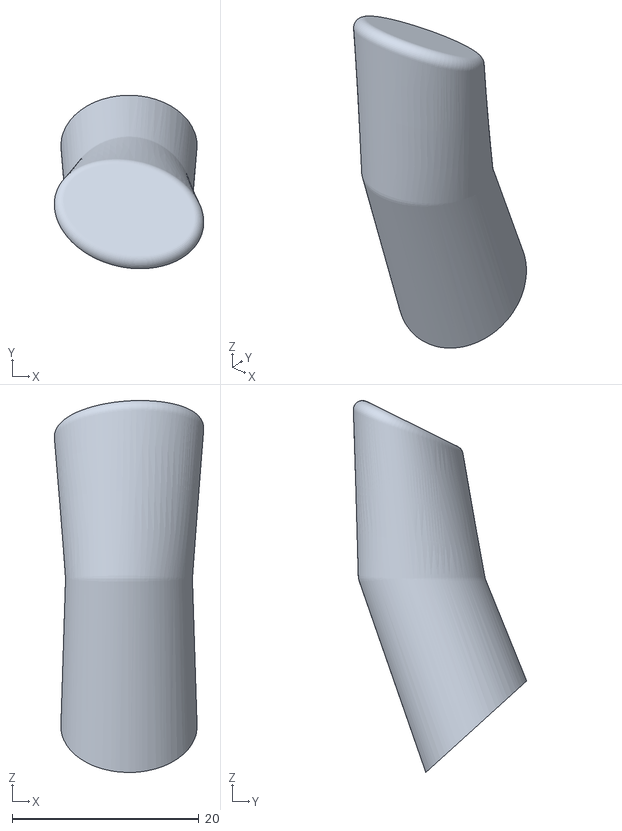
[picture p68: CAD file, 2024-01-24]
Mechanical design/Hand /STL/110_R/Thumb - 110_R.STL
16.0 x 18.6 x 39.9
