AILab-UniversityofTsukuba/Tsukuba-Open-Source-Hand-Prosthesis/Mechanical design/Hand /STL/115_R/Thumb - 115_R.STL

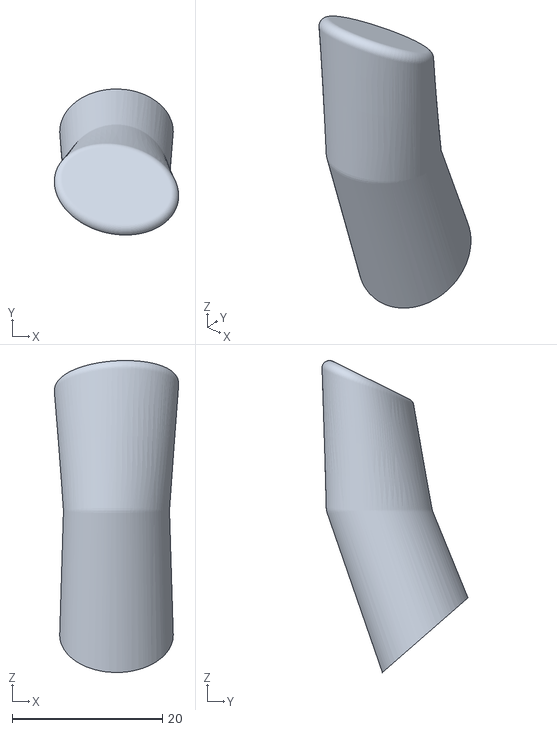
[picture p69: CAD file, 2024-01-24]
Mechanical design/Hand /STL/115_R/Thumb - 115_R.STL
16.5 x 19.4 x 41.5
