AILab-UniversityofTsukuba/Tsukuba-Open-Source-Hand-Prosthesis/Mechanical design/Hand /STL/120_R/Thenar eminence - 120_R.STL

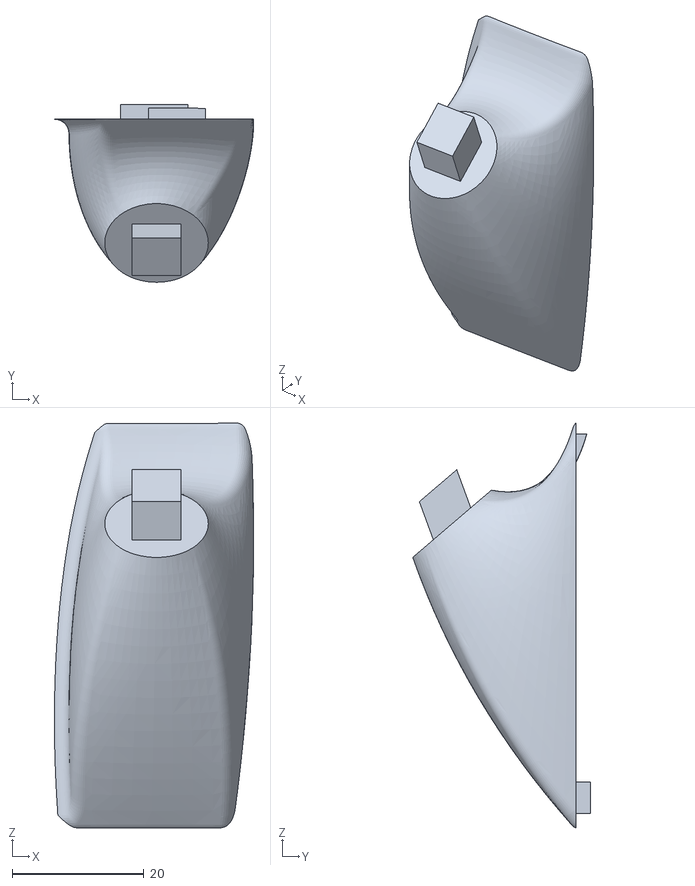
[picture p70: CAD file, 2024-01-24]
Mechanical design/Hand /STL/120_R/Thenar eminence - 120_R.STL
30.2 x 26.9 x 61.4
