AILab-UniversityofTsukuba/Tsukuba-Open-Source-Hand-Prosthesis/Mechanical design/Hand /STL/125_R/Lid - 125_R.STL

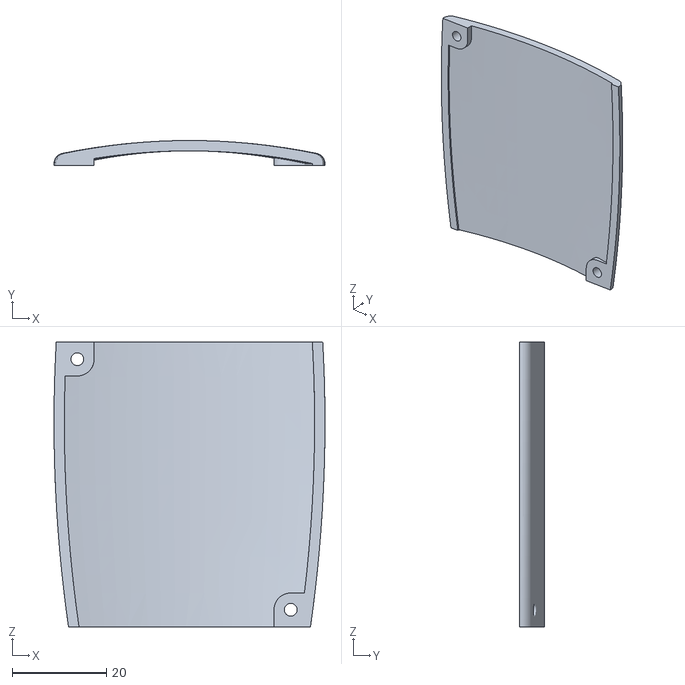
[picture p71: CAD file, 2024-01-24]
Mechanical design/Hand /STL/125_R/Lid - 125_R.STL
57.4 x 5.30 x 60.4
