AILab-UniversityofTsukuba/Tsukuba-Open-Source-Hand-Prosthesis/Mechanical design/Hand /STL/130_R/Thumb - 130_R.STL

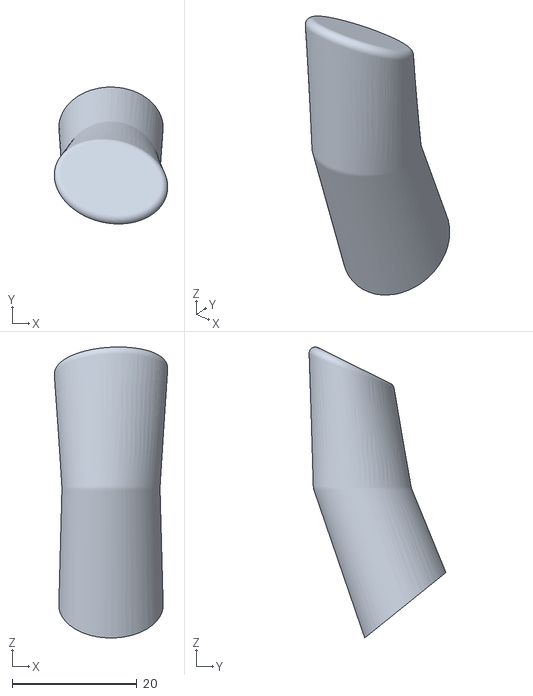
[picture p72: CAD file, 2024-01-24]
Mechanical design/Hand /STL/130_R/Thumb - 130_R.STL
18.1 x 21.9 x 46.6
