AILab-UniversityofTsukuba/Tsukuba-Open-Source-Hand-Prosthesis/Mechanical design/Hand /STL/135_R/Middle finger - 135_R.STL

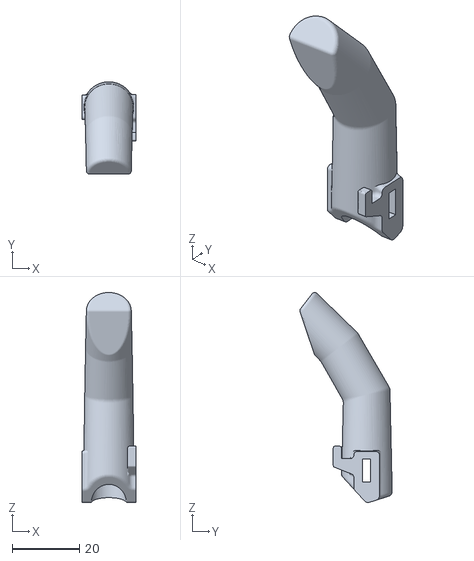
[picture p73: CAD file, 2024-01-24]
Mechanical design/Hand /STL/135_R/Middle finger - 135_R.STL
15.9 x 27.4 x 62.3
