AILab-UniversityofTsukuba/Tsukuba-Open-Source-Hand-Prosthesis/Mechanical design/Hand /STL/140_R/Index finger - 140_R.STL

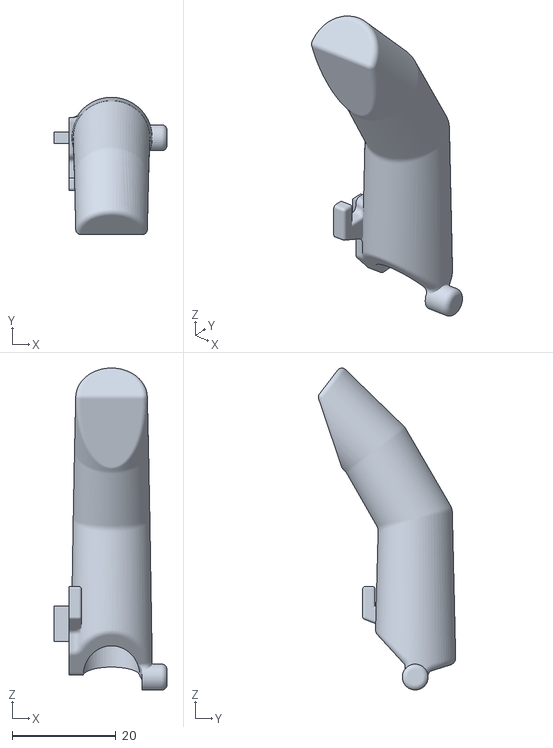
[picture p74: CAD file, 2024-01-24]
Mechanical design/Hand /STL/140_R/Index finger - 140_R.STL
21.8 x 26.5 x 62.1
