AILab-UniversityofTsukuba/Tsukuba-Open-Source-Hand-Prosthesis/Mechanical design/Hand /STL/145_R/Palm - 145_R.STL

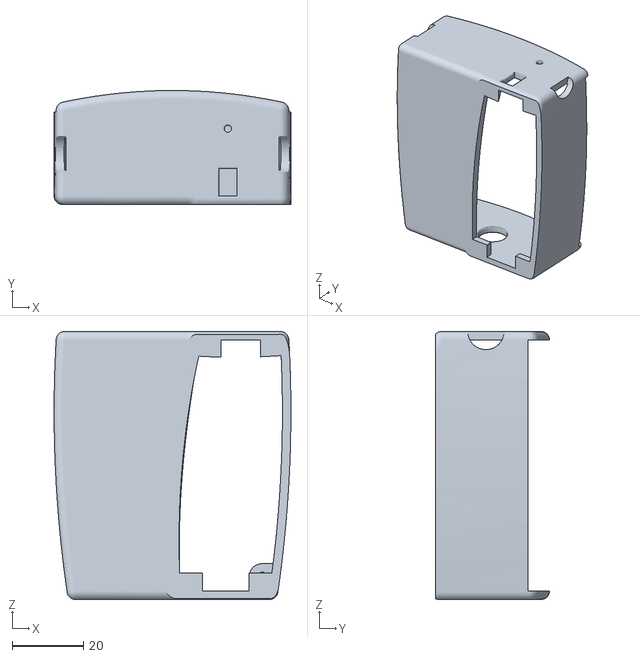
[picture p75: CAD file, 2024-01-24]
Mechanical design/Hand /STL/145_R/Palm - 145_R.STL
66.6 x 32.1 x 75.4
