AILab-UniversityofTsukuba/Tsukuba-Open-Source-Hand-Prosthesis/Mechanical design/Hand /STL/150_R/Rotation axis - 150_R.STL

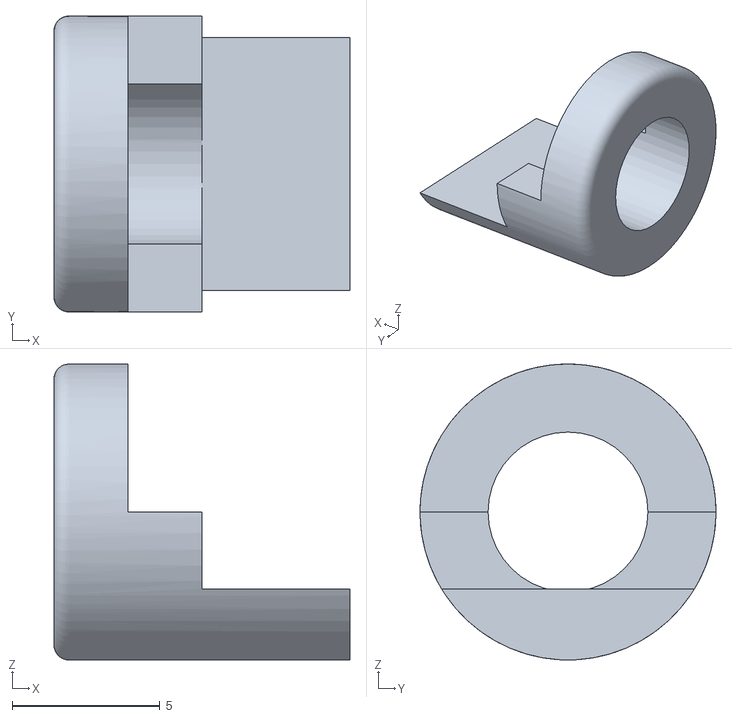
[picture p76: CAD file, 2024-01-24]
Mechanical design/Hand /STL/150_R/Rotation axis - 150_R.STL
10.0 x 10.0 x 10.0
