AILab-UniversityofTsukuba/Tsukuba-Open-Source-Hand-Prosthesis/Mechanical design/Hand /STL/100_R/Little finger - 100_R.STL

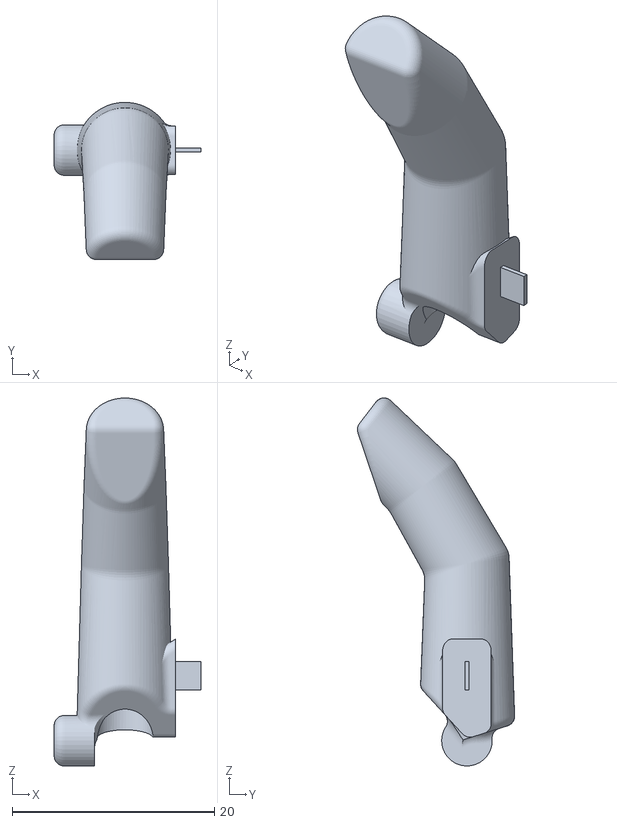
[picture p77: CAD file, 2024-01-24]
Mechanical design/Hand /STL/100_R/Little finger - 100_R.STL
14.5 x 15.5 x 36.4
