AILab-UniversityofTsukuba/Tsukuba-Open-Source-Hand-Prosthesis/Mechanical design/Hand /STL/105_R/Lid - 105_R.STL

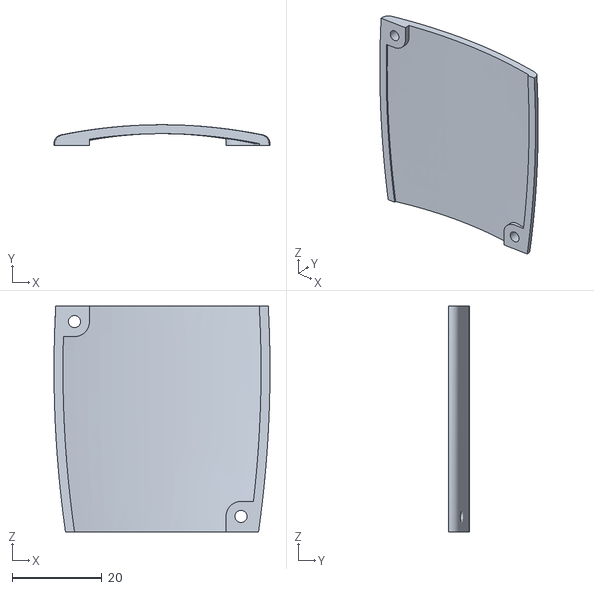
[picture p78: CAD file, 2024-01-24]
Mechanical design/Hand /STL/105_R/Lid - 105_R.STL
48.2 x 4.60 x 50.4
