AILab-UniversityofTsukuba/Tsukuba-Open-Source-Hand-Prosthesis/Mechanical design/Hand /STL/110_R/Little finger - 110_R.STL

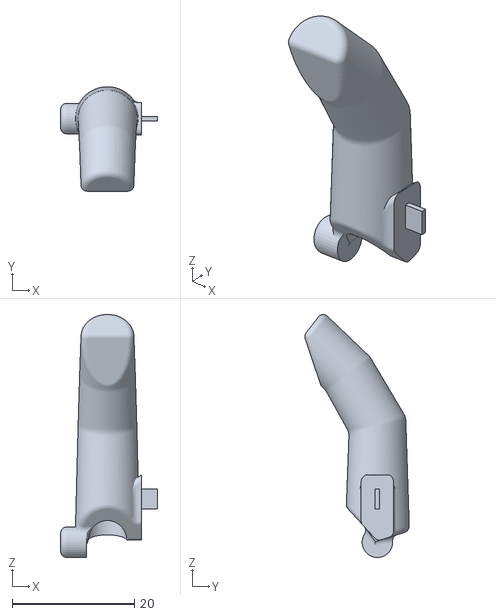
[picture p79: CAD file, 2024-01-24]
Mechanical design/Hand /STL/110_R/Little finger - 110_R.STL
15.8 x 17.1 x 39.7
