AILab-UniversityofTsukuba/Tsukuba-Open-Source-Hand-Prosthesis/Mechanical design/Hand /STL/115_R/Index finger - 115_R.STL

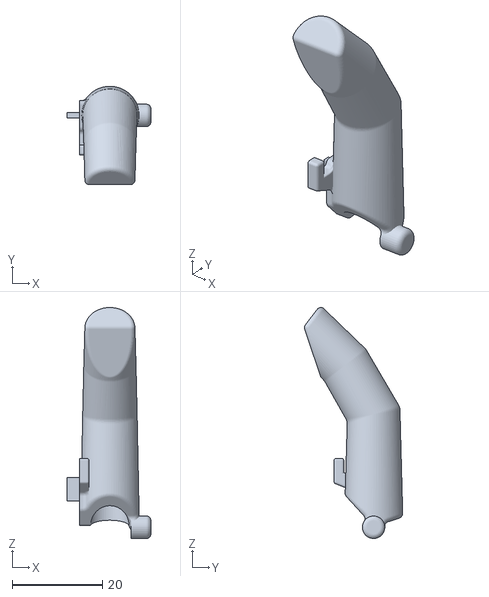
[picture p80: CAD file, 2024-01-24]
Mechanical design/Hand /STL/115_R/Index finger - 115_R.STL
18.6 x 21.9 x 51.3
