AILab-UniversityofTsukuba/Tsukuba-Open-Source-Hand-Prosthesis/Mechanical design/Hand /STL/120_R/Palm - 120_R.STL

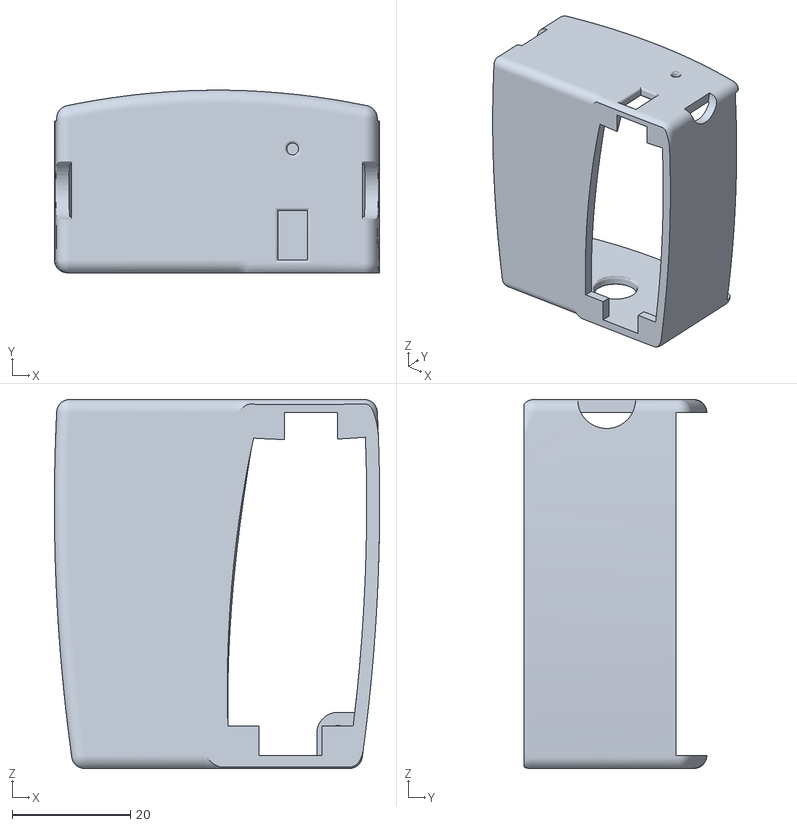
[picture p81: CAD file, 2024-01-24]
Mechanical design/Hand /STL/120_R/Palm - 120_R.STL
55.0 x 30.9 x 62.4
