AILab-UniversityofTsukuba/Tsukuba-Open-Source-Hand-Prosthesis/Mechanical design/Hand /STL/125_R/Palm - 125_R.STL

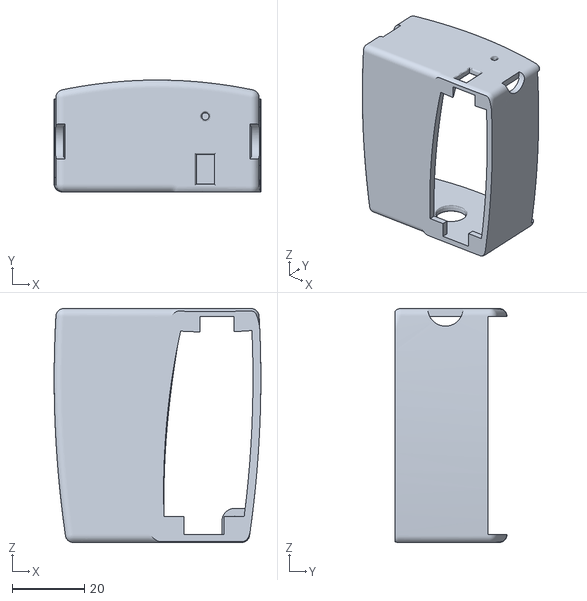
[picture p82: CAD file, 2024-01-24]
Mechanical design/Hand /STL/125_R/Palm - 125_R.STL
57.4 x 31.1 x 65.0
