AILab-UniversityofTsukuba/Tsukuba-Open-Source-Hand-Prosthesis/Mechanical design/Hand /STL/130_R/Palm - 130_R.STL

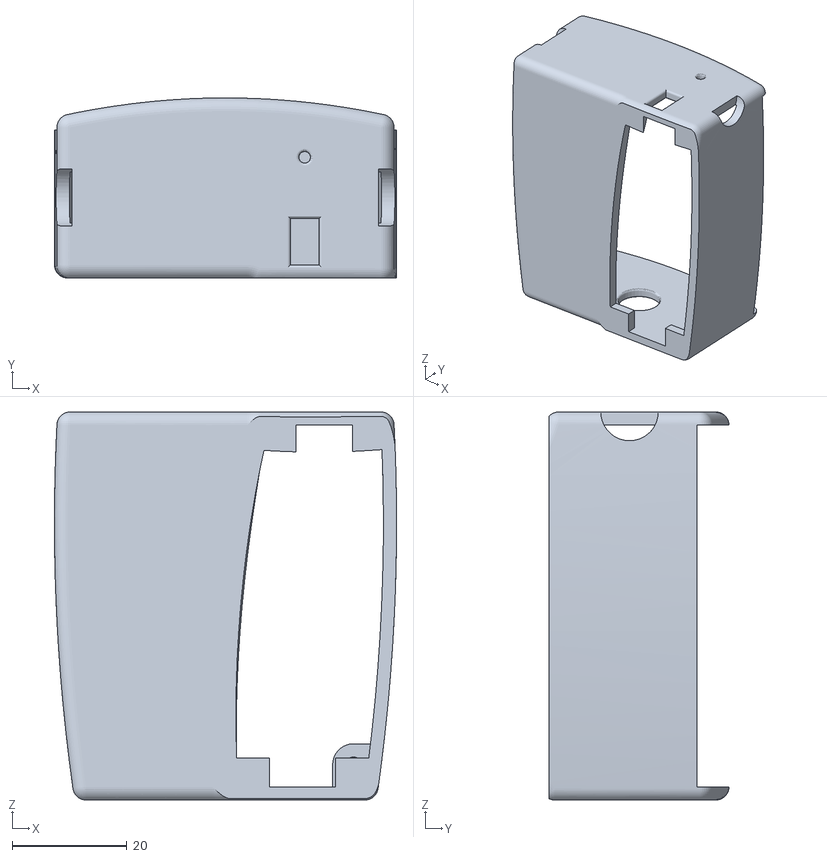
[picture p83: CAD file, 2024-01-24]
Mechanical design/Hand /STL/130_R/Palm - 130_R.STL
59.6 x 31.4 x 67.6
