AILab-UniversityofTsukuba/Tsukuba-Open-Source-Hand-Prosthesis/Mechanical design/Hand /STL/135_R/Thenar eminence - 135_R.STL

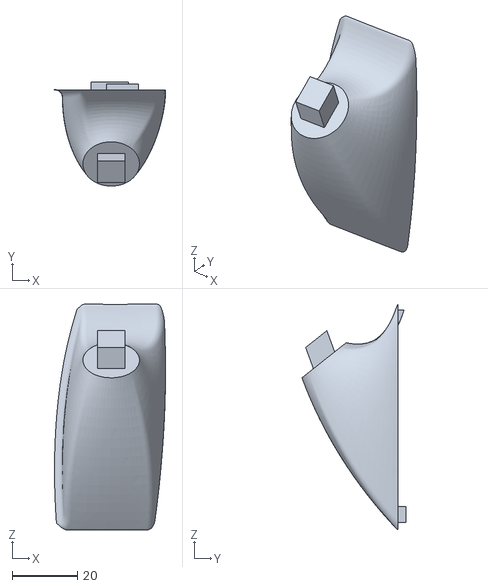
[picture p84: CAD file, 2024-01-24]
Mechanical design/Hand /STL/135_R/Thenar eminence - 135_R.STL
34.0 x 31.9 x 69.2
