AILab-UniversityofTsukuba/Tsukuba-Open-Source-Hand-Prosthesis/Mechanical design/Hand /STL/140_R/Lid - 140_R.STL

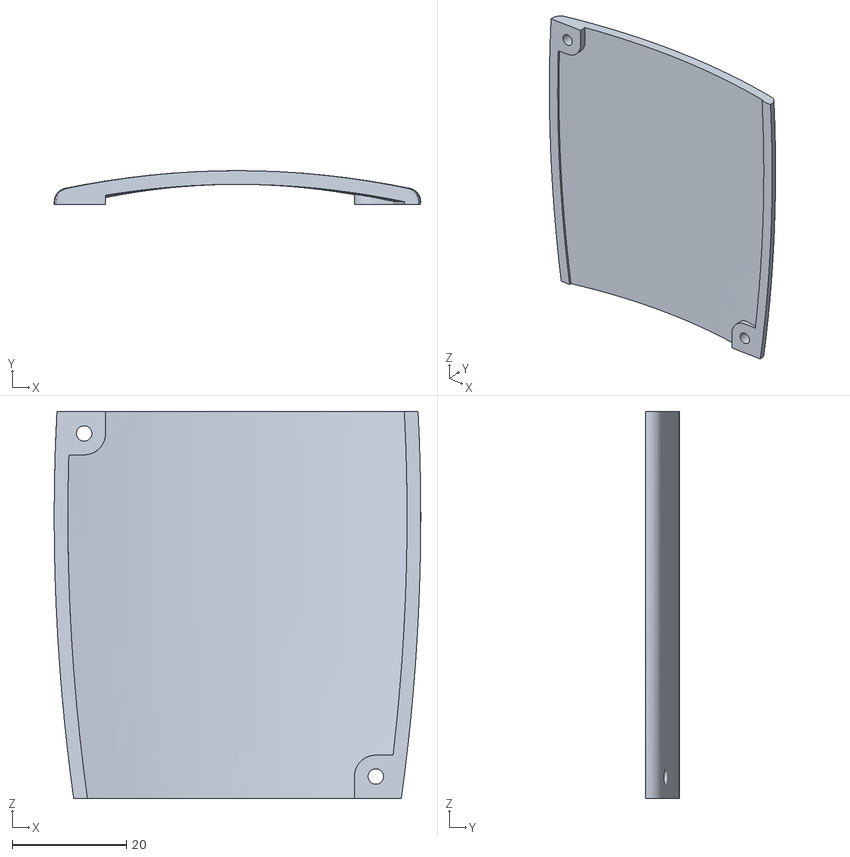
[picture p85: CAD file, 2024-01-24]
Mechanical design/Hand /STL/140_R/Lid - 140_R.STL
64.2 x 5.90 x 67.8
