AILab-UniversityofTsukuba/Tsukuba-Open-Source-Hand-Prosthesis/Mechanical design/Hand /STL/145_R/Thumb - 145_R.STL

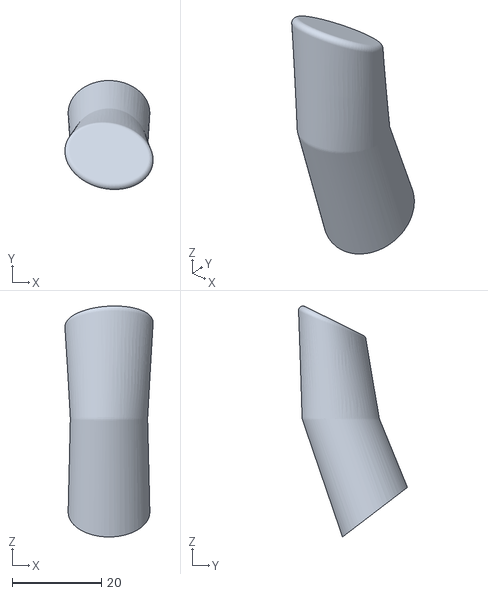
[picture p86: CAD file, 2024-01-24]
Mechanical design/Hand /STL/145_R/Thumb - 145_R.STL
19.7 x 24.4 x 51.7
