AILab-UniversityofTsukuba/Tsukuba-Open-Source-Hand-Prosthesis/Mechanical design/Hand /STL/150_R/Palm - 150_R.STL

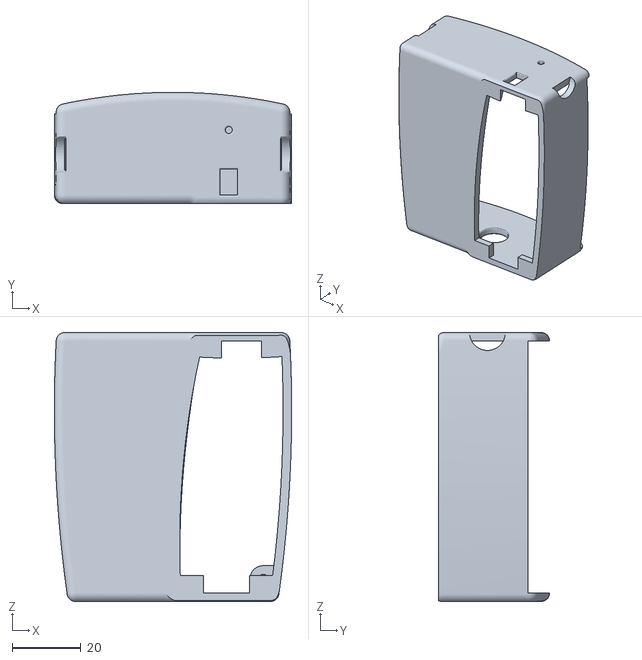
[picture p87: CAD file, 2024-01-24]
Mechanical design/Hand /STL/150_R/Palm - 150_R.STL
68.8 x 32.3 x 78.0
