AILab-UniversityofTsukuba/Tsukuba-Open-Source-Hand-Prosthesis/Mechanical design/Hand /STL/100_R/Palm - 100_R.STL

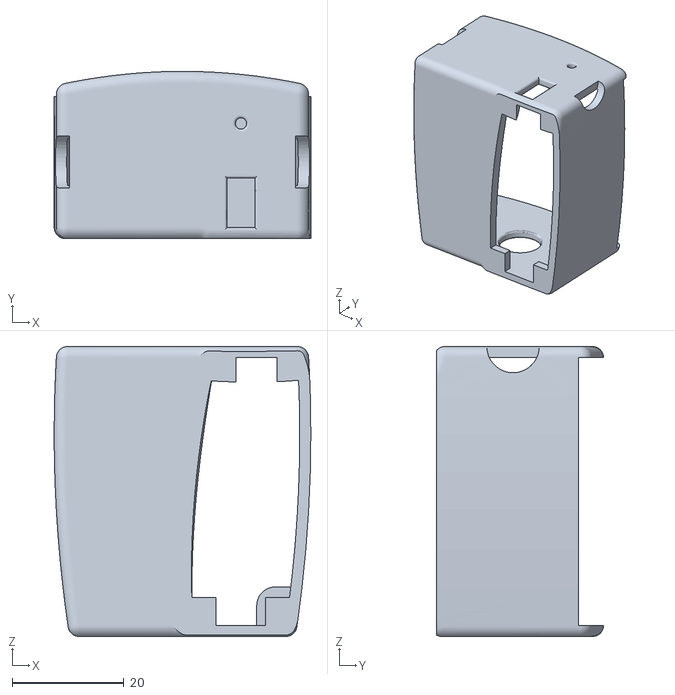
[picture p88: CAD file, 2024-01-24]
Mechanical design/Hand /STL/100_R/Palm - 100_R.STL
46.0 x 30.0 x 52.0
