AILab-UniversityofTsukuba/Tsukuba-Open-Source-Hand-Prosthesis/Mechanical design/Hand /STL/105_R/Index finger - 105_R.STL

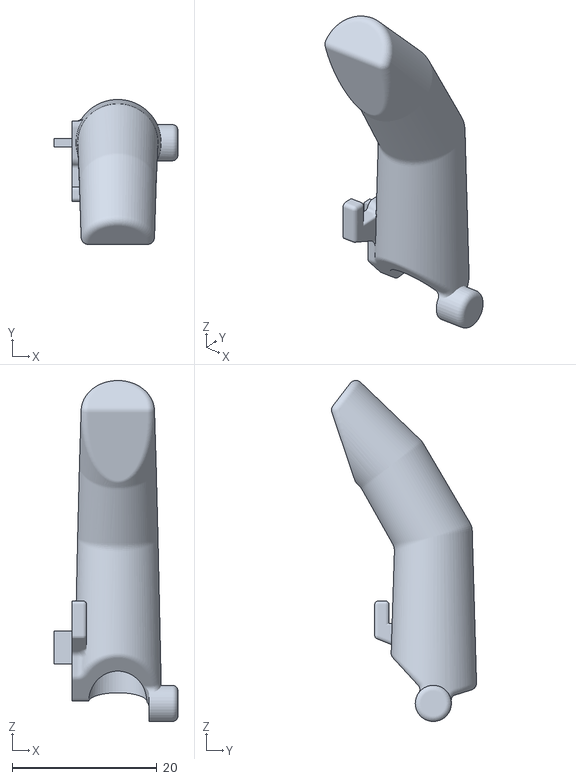
[picture p89: CAD file, 2024-01-24]
Mechanical design/Hand /STL/105_R/Index finger - 105_R.STL
17.1 x 20.0 x 47.1
