AILab-UniversityofTsukuba/Tsukuba-Open-Source-Hand-Prosthesis/Mechanical design/Hand /STL/110_R/Index finger - 110_R.STL

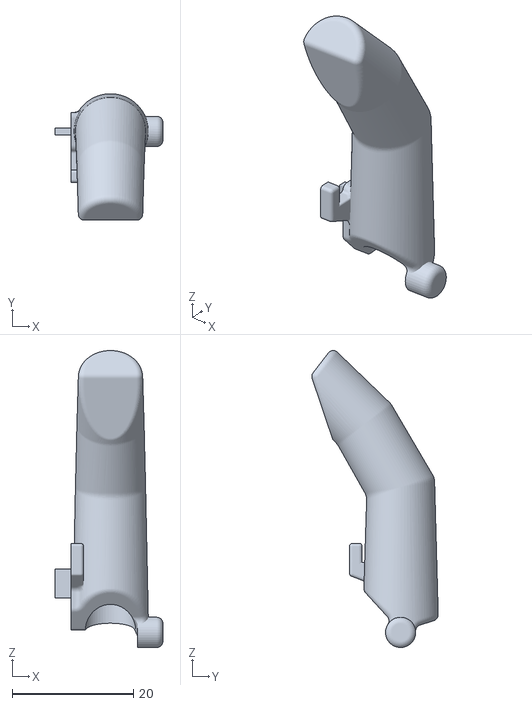
[picture p90: CAD file, 2024-01-24]
Mechanical design/Hand /STL/110_R/Index finger - 110_R.STL
17.8 x 20.9 x 49.1
