AILab-UniversityofTsukuba/Tsukuba-Open-Source-Hand-Prosthesis/Mechanical design/Hand /STL/115_R/Lid - 115_R.STL

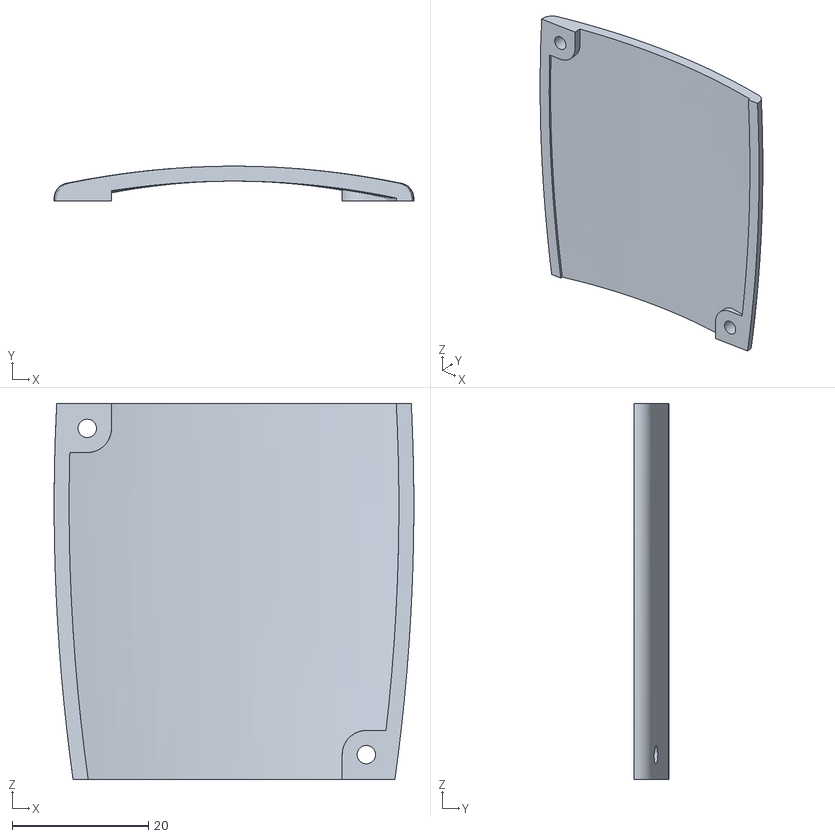
[picture p91: CAD file, 2024-01-24]
Mechanical design/Hand /STL/115_R/Lid - 115_R.STL
52.8 x 5.10 x 55.2
