AILab-UniversityofTsukuba/Tsukuba-Open-Source-Hand-Prosthesis/Mechanical design/Hand /STL/120_R/Middle finger - 120_R.STL

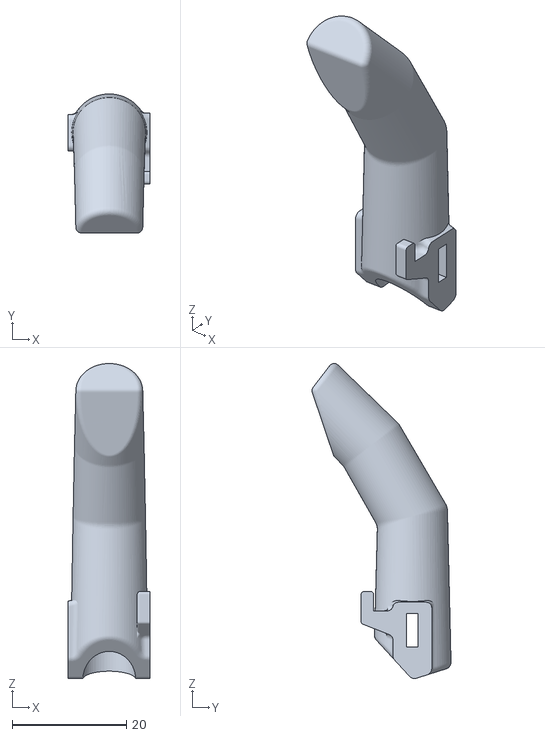
[picture p92: CAD file, 2024-01-24]
Mechanical design/Hand /STL/120_R/Middle finger - 120_R.STL
14.3 x 24.4 x 55.2
