AILab-UniversityofTsukuba/Tsukuba-Open-Source-Hand-Prosthesis/Mechanical design/Hand /STL/125_R/Little finger - 125_R.STL

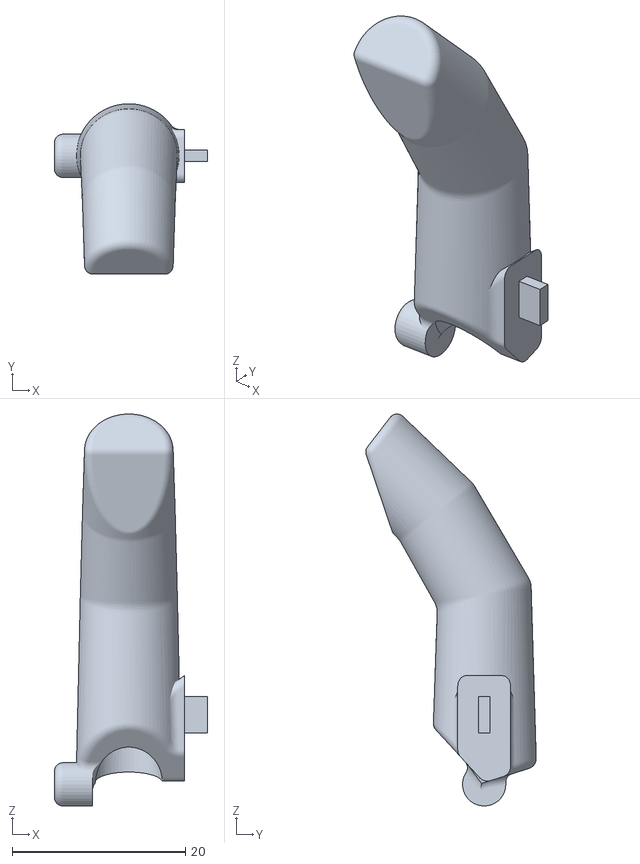
[picture p93: CAD file, 2024-01-24]
Mechanical design/Hand /STL/125_R/Little finger - 125_R.STL
17.7 x 19.7 x 45.3
