AILab-UniversityofTsukuba/Tsukuba-Open-Source-Hand-Prosthesis/Mechanical design/Hand /STL/130_R/Middle finger - 130_R.STL

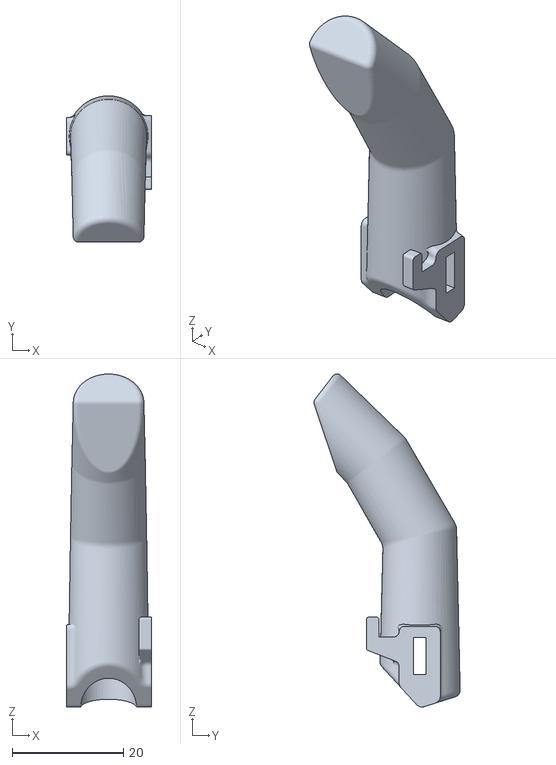
[picture p94: CAD file, 2024-01-24]
Mechanical design/Hand /STL/130_R/Middle finger - 130_R.STL
15.3 x 26.3 x 59.9
