AILab-UniversityofTsukuba/Tsukuba-Open-Source-Hand-Prosthesis/Mechanical design/Hand /STL/135_R/Index finger - 135_R.STL

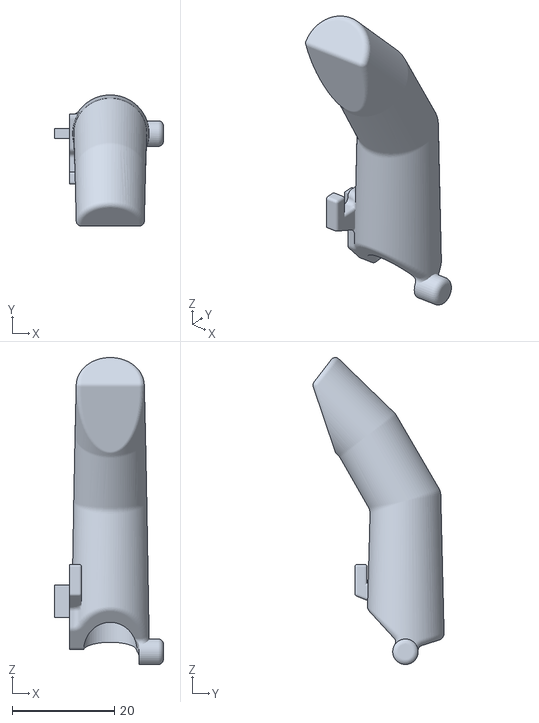
[picture p95: CAD file, 2024-01-24]
Mechanical design/Hand /STL/135_R/Index finger - 135_R.STL
21.3 x 25.7 x 60.1
