AILab-UniversityofTsukuba/Tsukuba-Open-Source-Hand-Prosthesis/Mechanical design/Hand /STL/140_R/Little finger - 140_R.STL

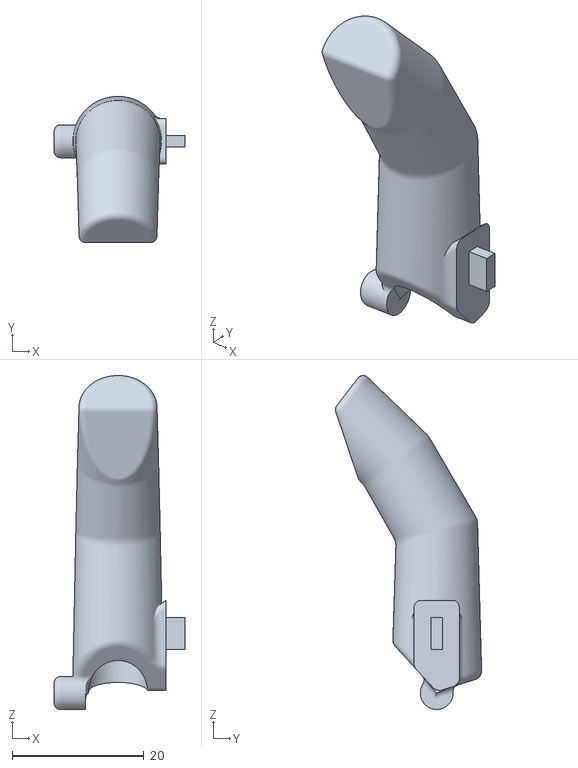
[picture p96: CAD file, 2024-01-24]
Mechanical design/Hand /STL/140_R/Little finger - 140_R.STL
19.9 x 22.2 x 50.6
