AILab-UniversityofTsukuba/Tsukuba-Open-Source-Hand-Prosthesis/Mechanical design/Hand /STL/145_R/Index finger - 145_R.STL

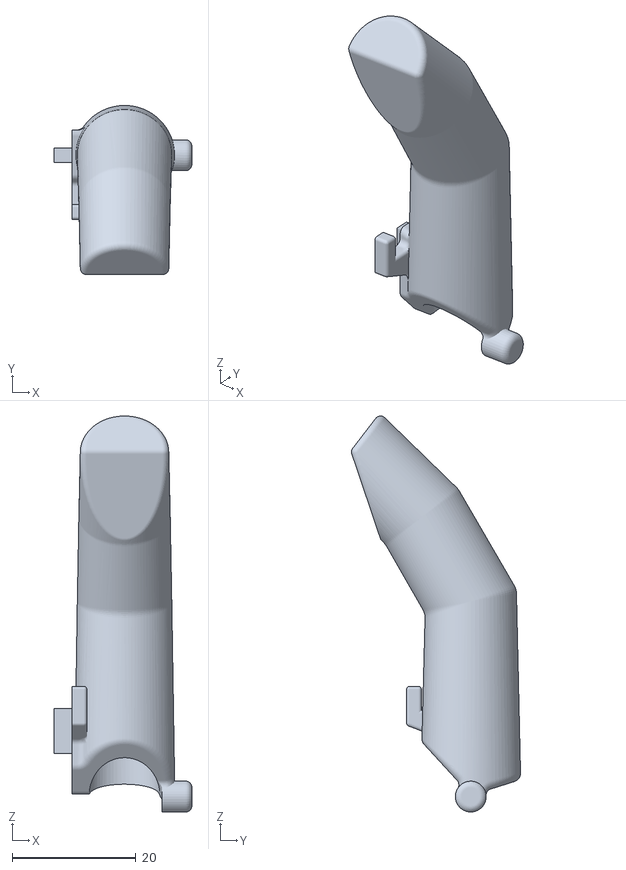
[picture p97: CAD file, 2024-01-24]
Mechanical design/Hand /STL/145_R/Index finger - 145_R.STL
22.3 x 27.4 x 64.1
