AILab-UniversityofTsukuba/Tsukuba-Open-Source-Hand-Prosthesis/Mechanical design/Hand /STL/150_R/Thumb - 150_R.STL

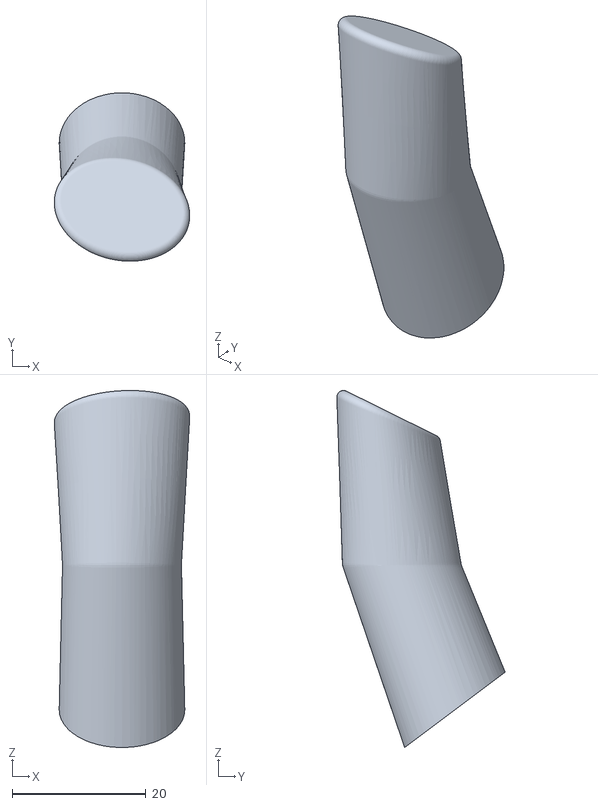
[picture p98: CAD file, 2024-01-24]
Mechanical design/Hand /STL/150_R/Thumb - 150_R.STL
20.3 x 25.2 x 53.4
