AILab-UniversityofTsukuba/Tsukuba-Open-Source-Hand-Prosthesis/Mechanical design/Hand /STL/100_R/Ring finger - 100_R.STL

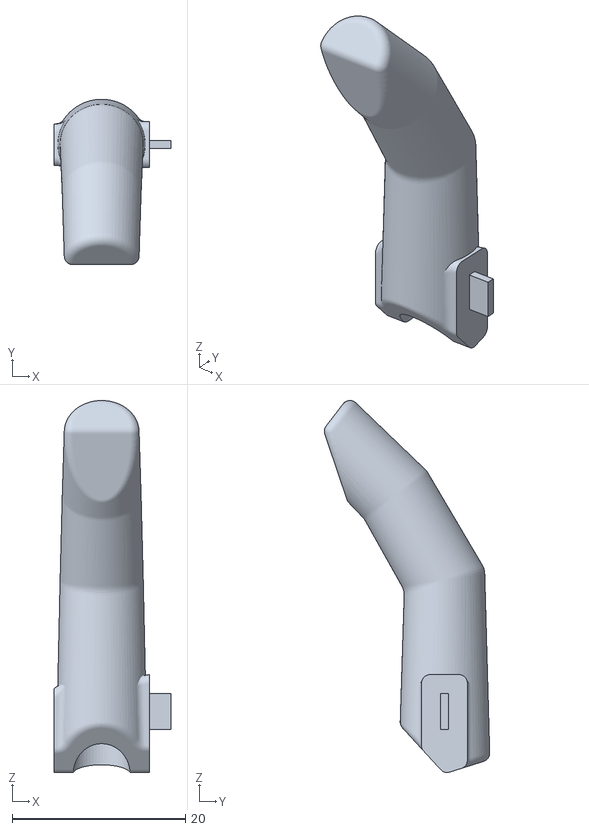
[picture p99: CAD file, 2024-01-24]
Mechanical design/Hand /STL/100_R/Ring finger - 100_R.STL
13.5 x 19.1 x 42.9
