AILab-UniversityofTsukuba/Tsukuba-Open-Source-Hand-Prosthesis/Mechanical design/Hand /STL/105_R/Little finger - 105_R.STL

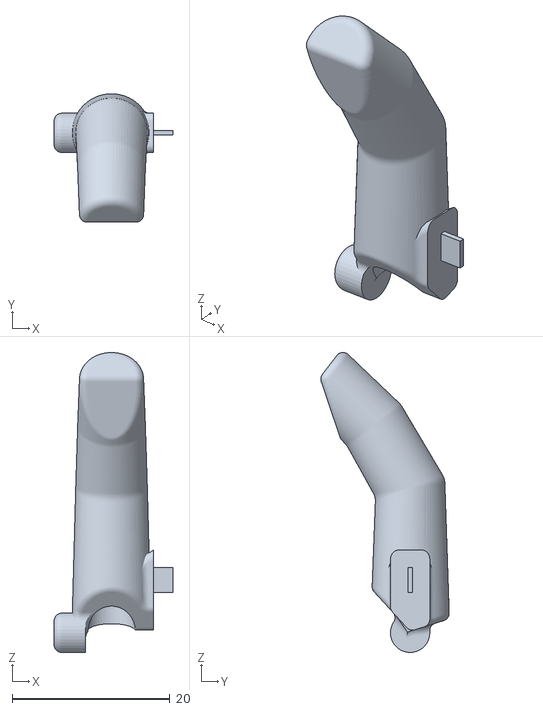
[picture p100: CAD file, 2024-01-24]
Mechanical design/Hand /STL/105_R/Little finger - 105_R.STL
15.1 x 16.3 x 38.1
