AILab-UniversityofTsukuba/Tsukuba-Open-Source-Hand-Prosthesis/Mechanical design/Hand /STL/110_R/Middle finger - 110_R.STL

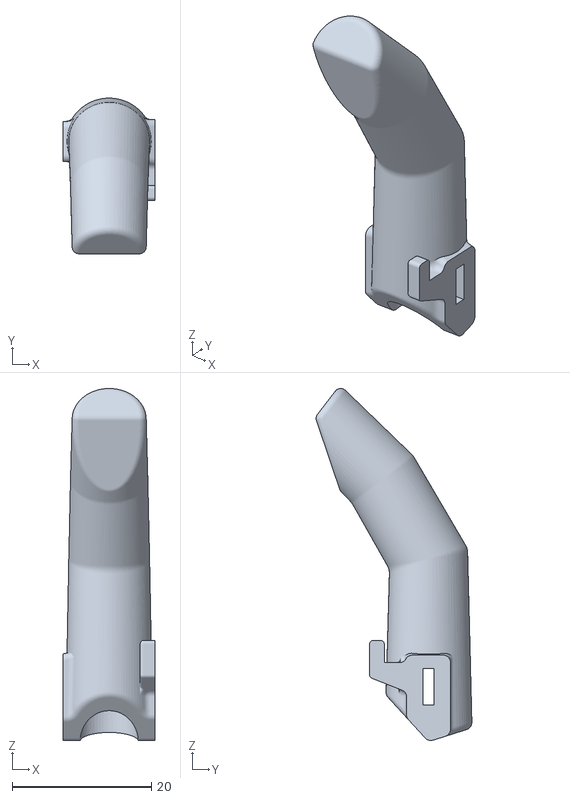
[picture p101: CAD file, 2024-01-24]
Mechanical design/Hand /STL/110_R/Middle finger - 110_R.STL
13.1 x 22.4 x 50.5
