AILab-UniversityofTsukuba/Tsukuba-Open-Source-Hand-Prosthesis/Mechanical design/Hand /STL/115_R/Palm - 115_R.STL

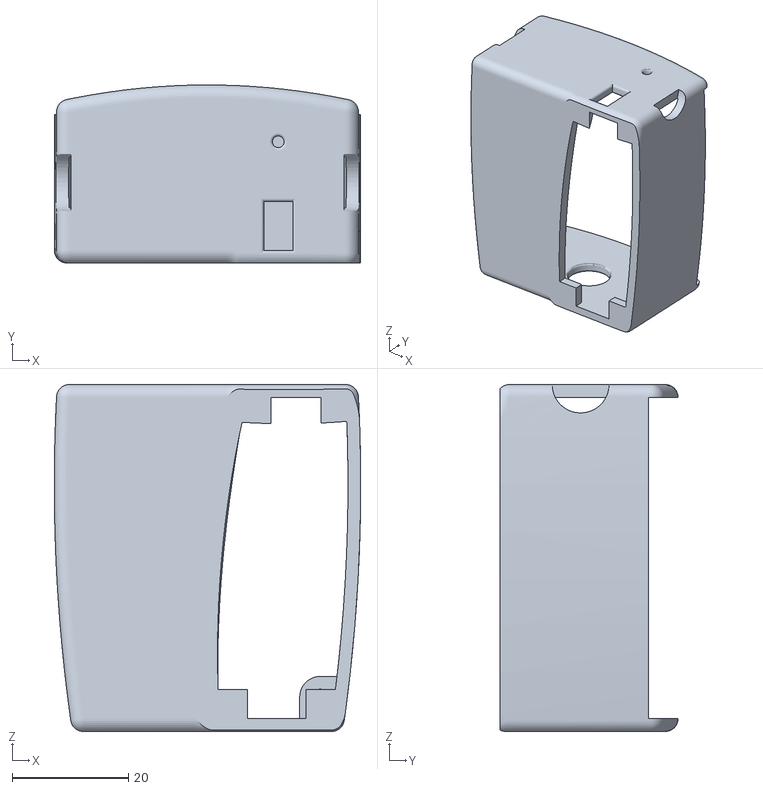
[picture p102: CAD file, 2024-01-24]
Mechanical design/Hand /STL/115_R/Palm - 115_R.STL
52.8 x 30.7 x 59.8
