AILab-UniversityofTsukuba/Tsukuba-Open-Source-Hand-Prosthesis/Mechanical design/Hand /STL/120_R/Little finger - 120_R.STL

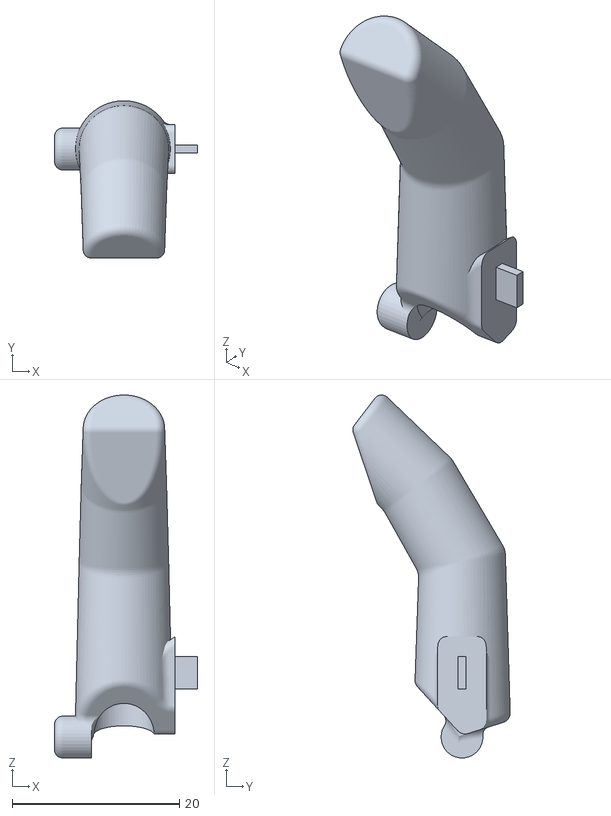
[picture p103: CAD file, 2024-01-24]
Mechanical design/Hand /STL/120_R/Little finger - 120_R.STL
17.1 x 18.8 x 43.4
