AILab-UniversityofTsukuba/Tsukuba-Open-Source-Hand-Prosthesis/Mechanical design/Hand /STL/130_R/Thenar eminence - 130_R.STL

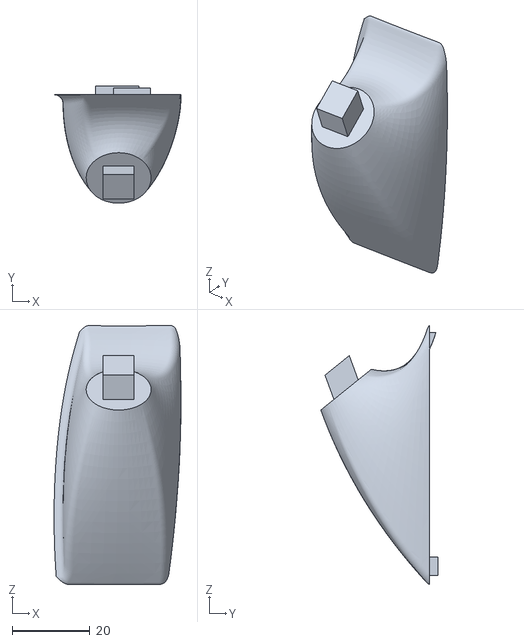
[picture p104: CAD file, 2024-01-24]
Mechanical design/Hand /STL/130_R/Thenar eminence - 130_R.STL
32.6 x 30.2 x 66.6
