AILab-UniversityofTsukuba/Tsukuba-Open-Source-Hand-Prosthesis/Mechanical design/Hand /STL/145_R/Thena eminence - 145_R.STL

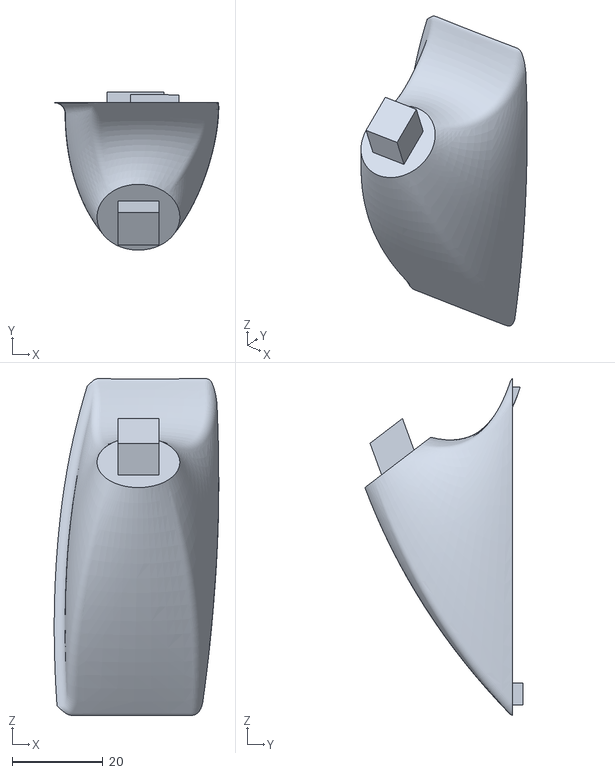
[picture p105: CAD file, 2024-01-24]
Mechanical design/Hand /STL/145_R/Thena eminence - 145_R.STL
36.3 x 34.9 x 74.4
