AILab-UniversityofTsukuba/Tsukuba-Open-Source-Hand-Prosthesis/Mechanical design/Hand /STL/150_R/Middle finger - 150_R.STL

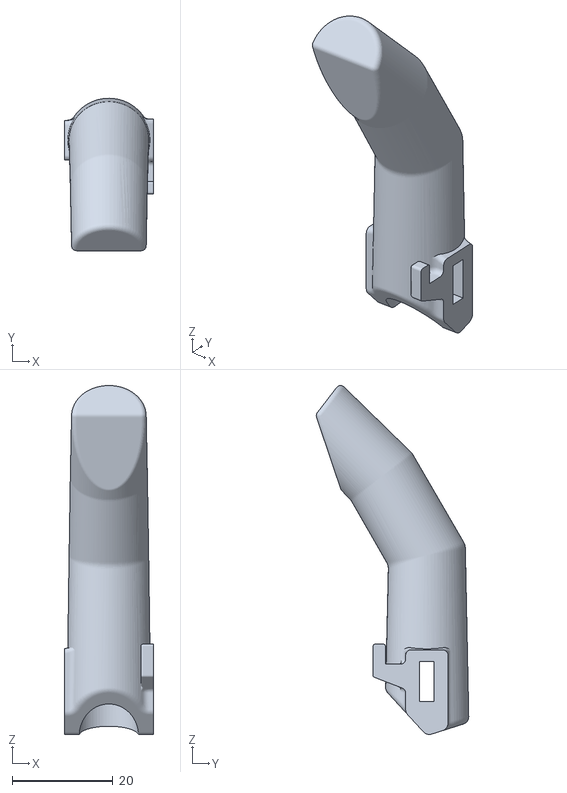
[picture p106: CAD file, 2024-01-24]
Mechanical design/Hand /STL/150_R/Middle finger - 150_R.STL
17.6 x 30.3 x 69.3
